ClevaPolytech/Arduino-Project/OralFinal/PolyShop.pdf

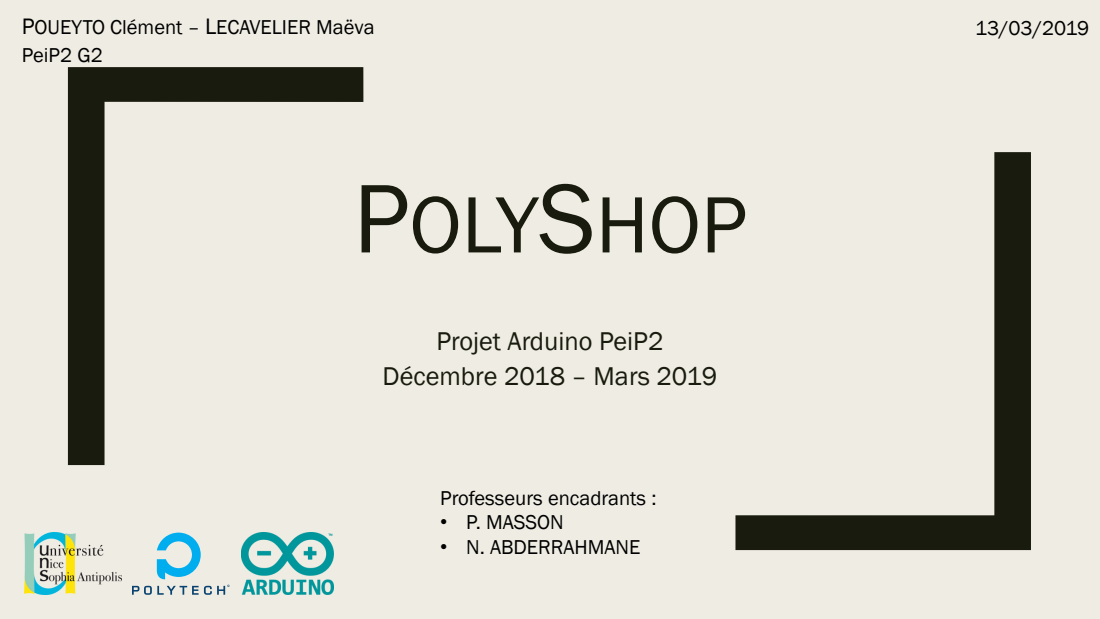
[picture p85: page 1]
POLYSHOP; Projet Arduino PeiP2 Décembre 2018 – Mars 2019; Professeurs encadrants : • P. MASSON • N. ABDERRAHMANE

POUEYTO Clément – LECAVELIER Maëva
PeiP2 G2

## Sommaire

■ Notre sujet
■ Objectifs initiaux
■ Comment ça fonctionne ?
■ De l’idée à la conception ■ Plannings
■ Conclusion

Notre sujet

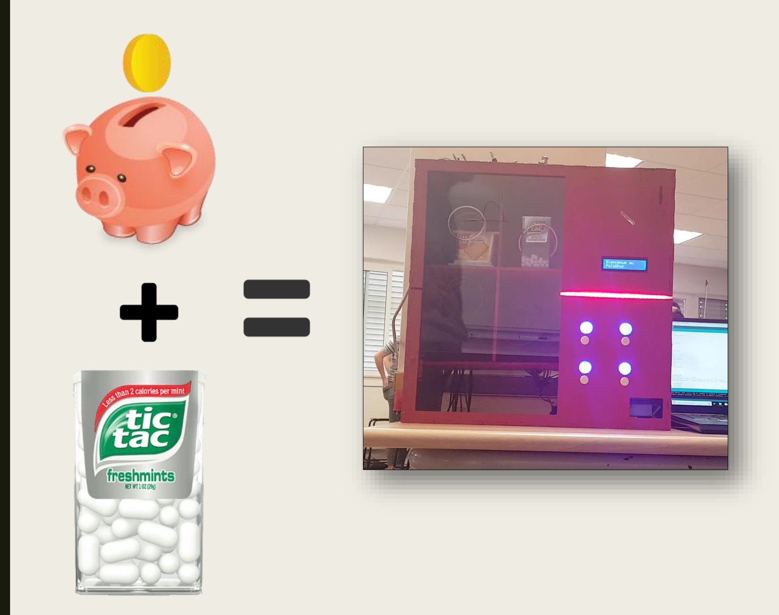
[picture p86: figure]

Monnayeur
Lumière
Barre de chargement
Ecran LCD
Distributeur de nourriture
Possibilité de sélectionner le snack voulu

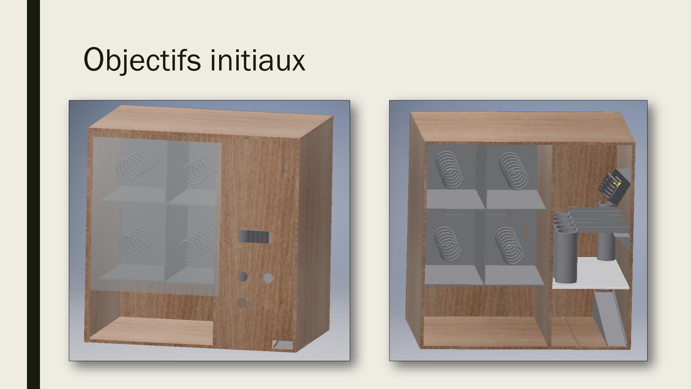
[picture p87: page 4]

Objectifs initiaux

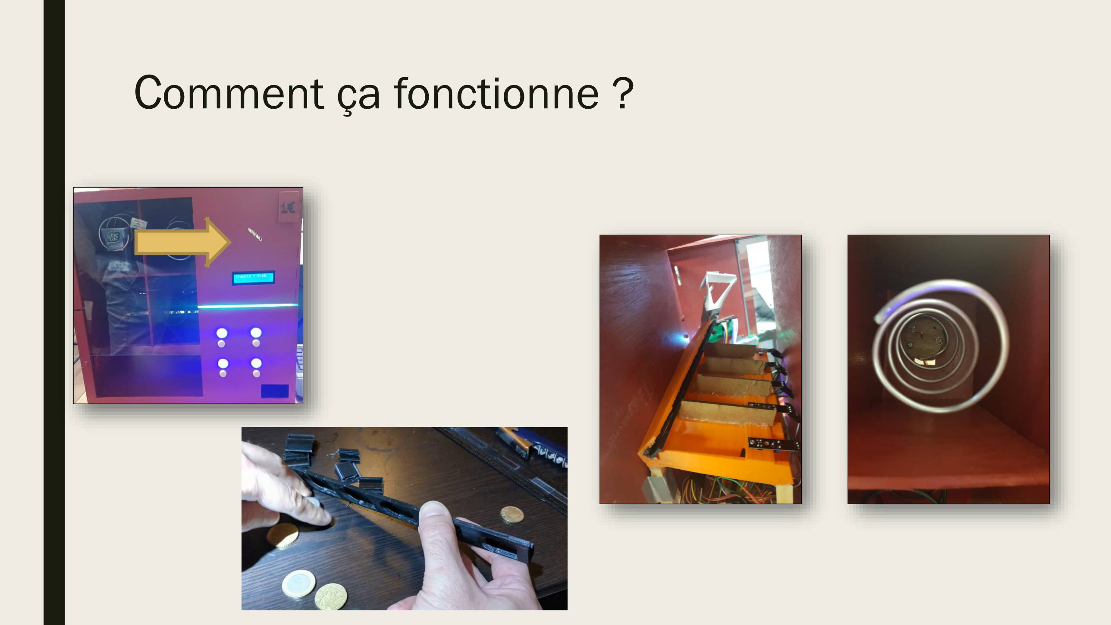
[picture p88: page 5]

Comment ça fonctionne ?

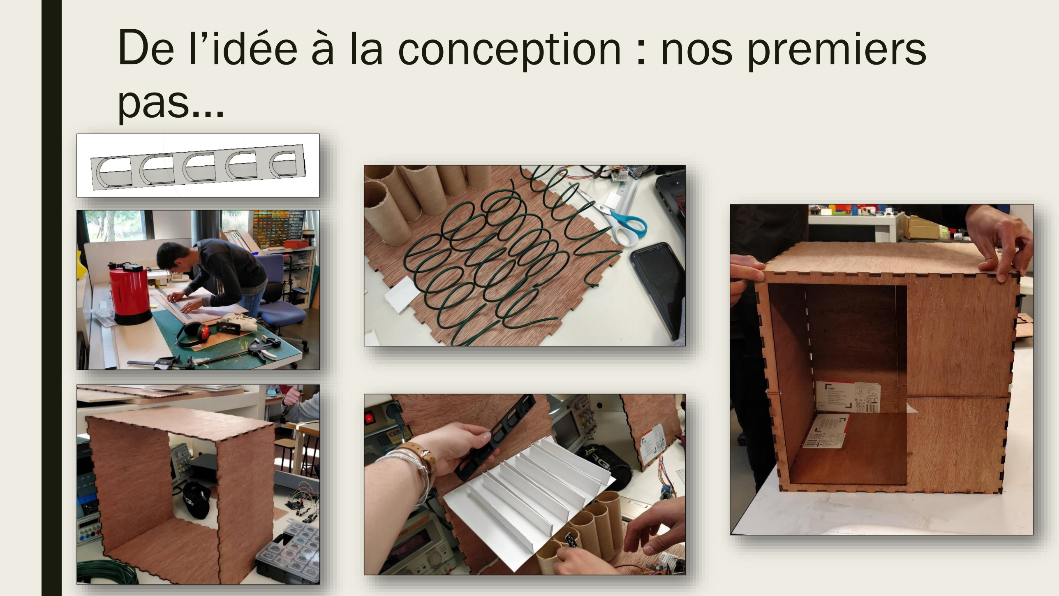
[picture p89: page 6]

De l’idée à la conception : nos premiers pas…

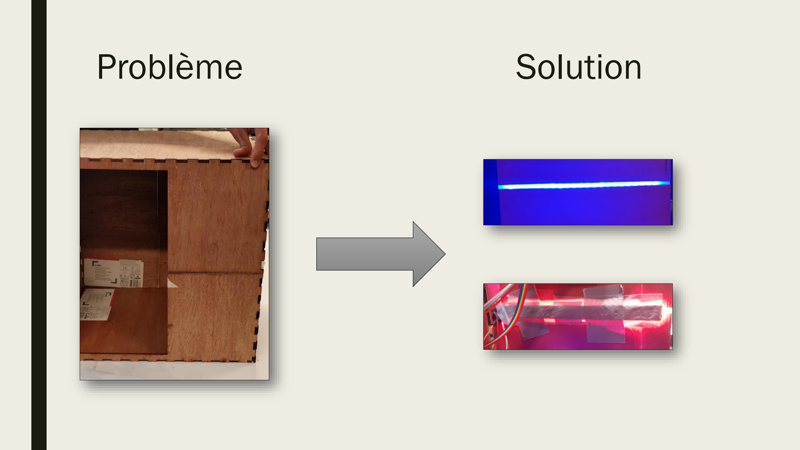
[picture p90: page 7]

Problème | Solution

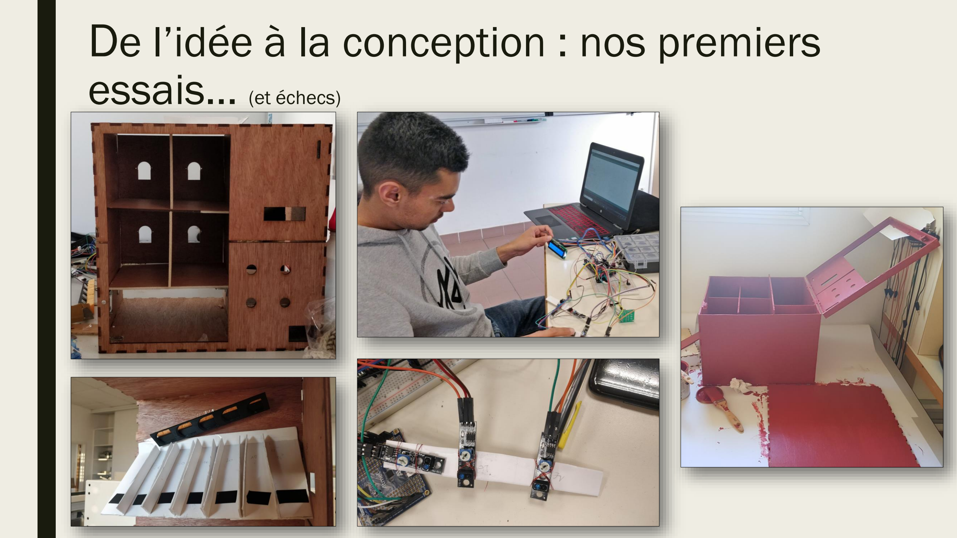
[picture p91: page 8]

De l’idée à la conception : nos premiers

essais… (et échecs)

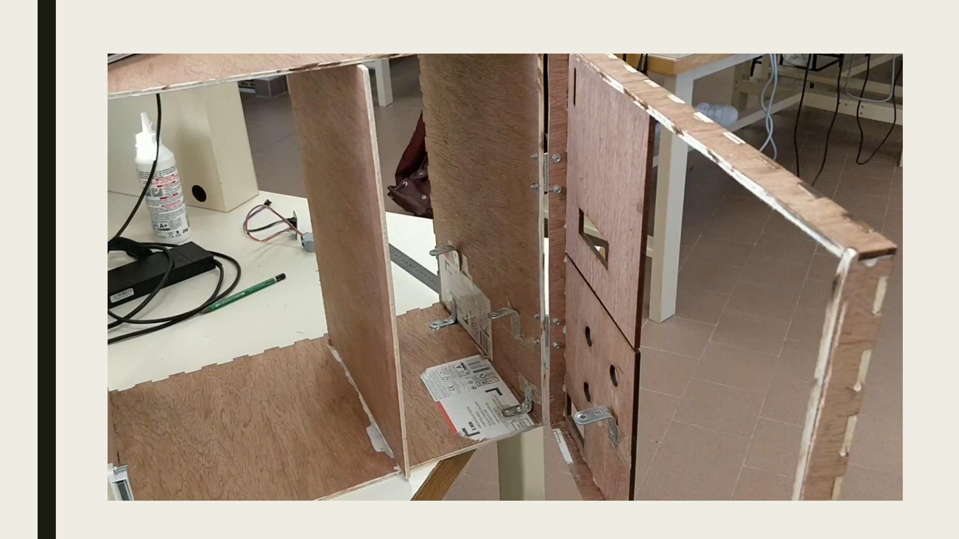
[picture p92: page 9]

Problème | Solution

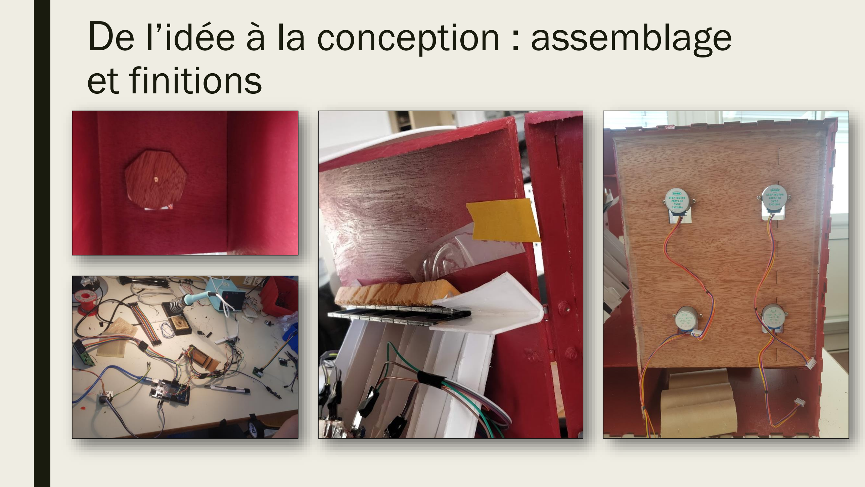
[picture p93: page 10]

De l’idée à la conception : assemblage et finitions

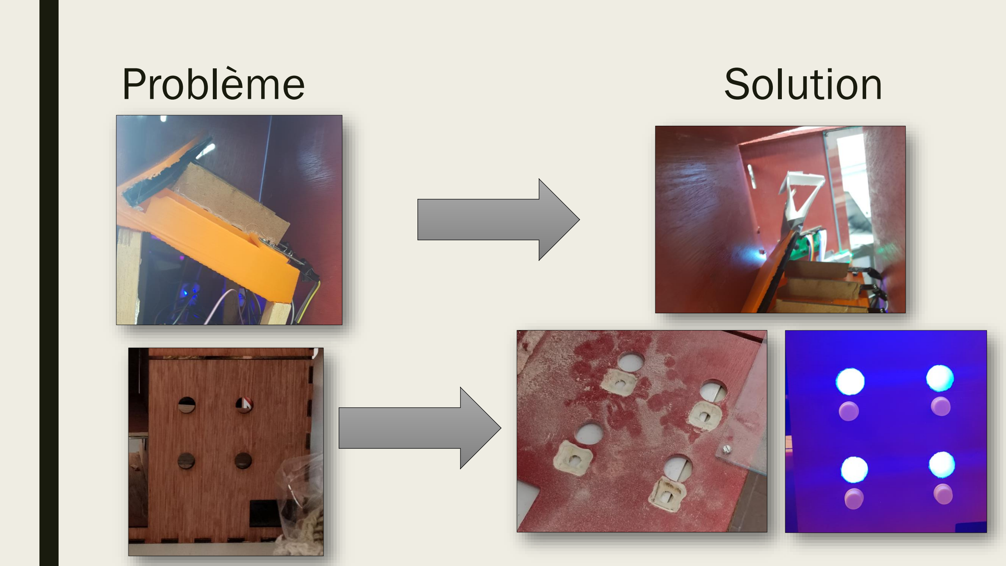
[picture p94: page 11]

Problème | Solution

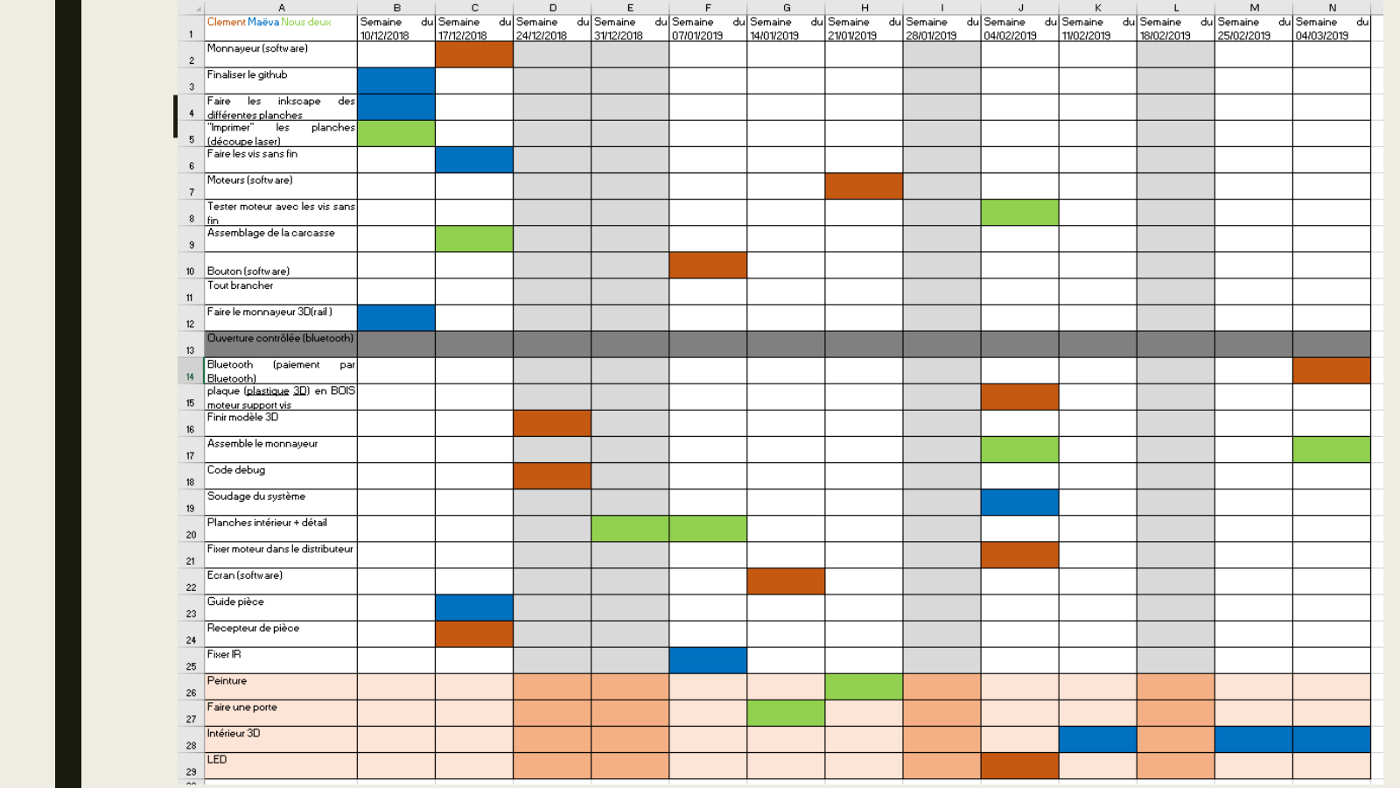
[picture p95: page 12]

Plannings

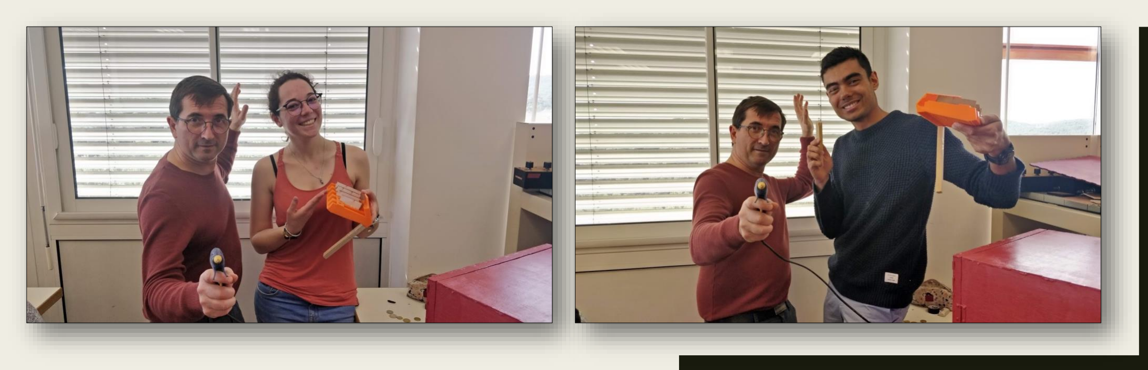
[picture p96: figure]

### CONCLUSION
