ClevaPolytech/Arduino-Project/Plannings/planning_initial.pdf

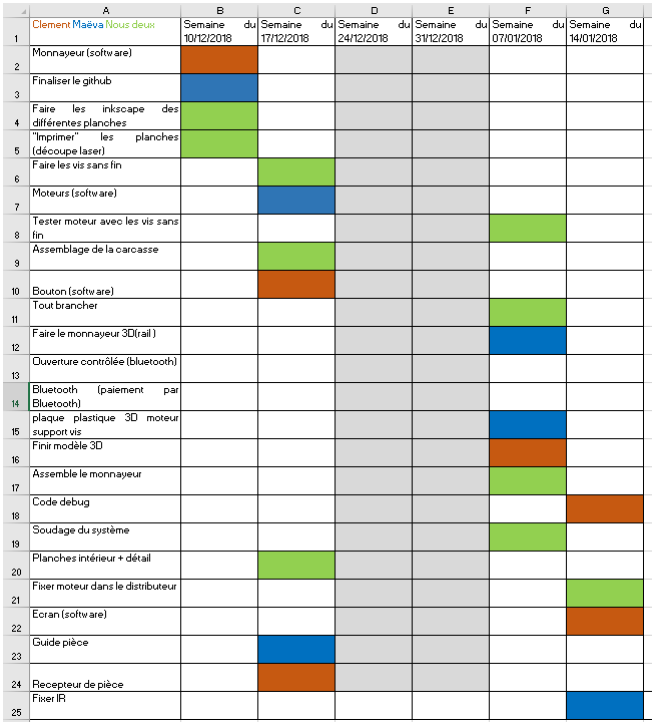
[picture p115: figure]
