ClevaPolytech/Arduino-Project/Photos/20181210_143604.jpg

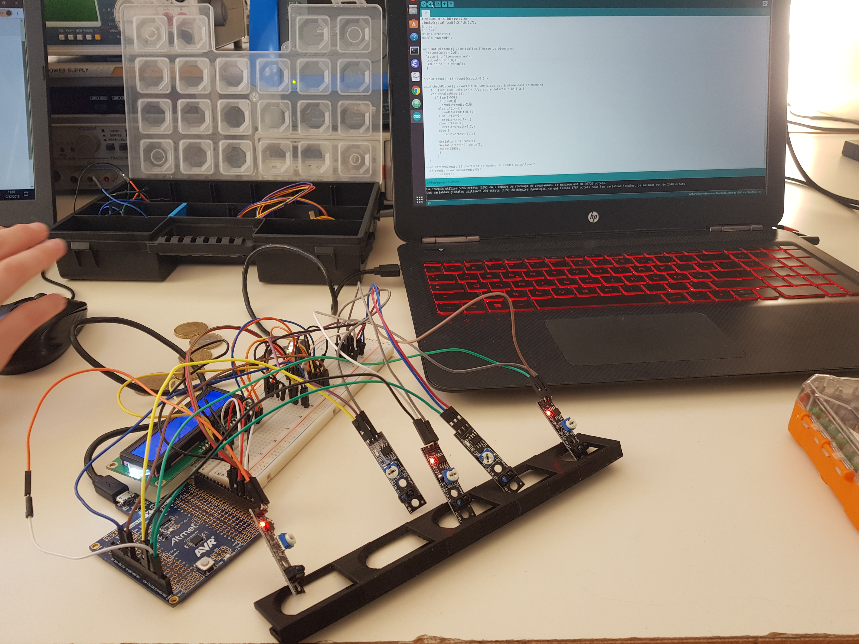
Photos/20181210_143604.jpg
