ClevaPolytech/Arduino-Project/Photos/20181210_154950.jpg

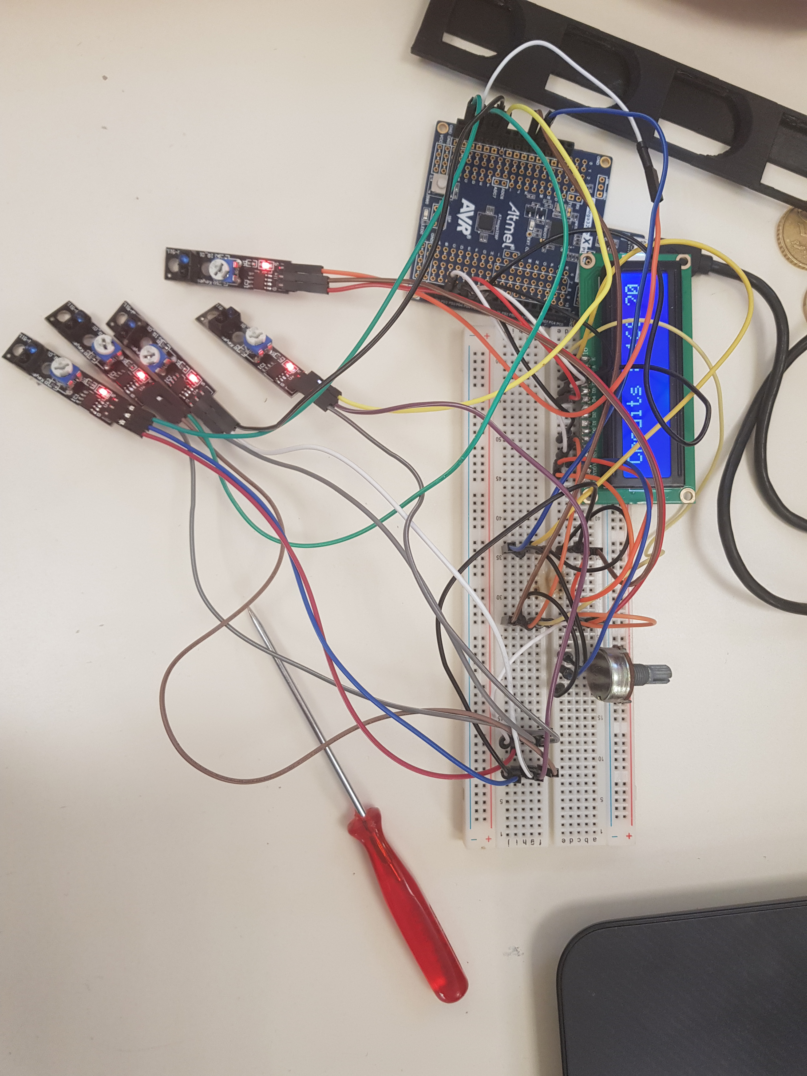
Photos/20181210_154950.jpg
