ClevaPolytech/Arduino-Project/Photos/20181214_130924.jpg

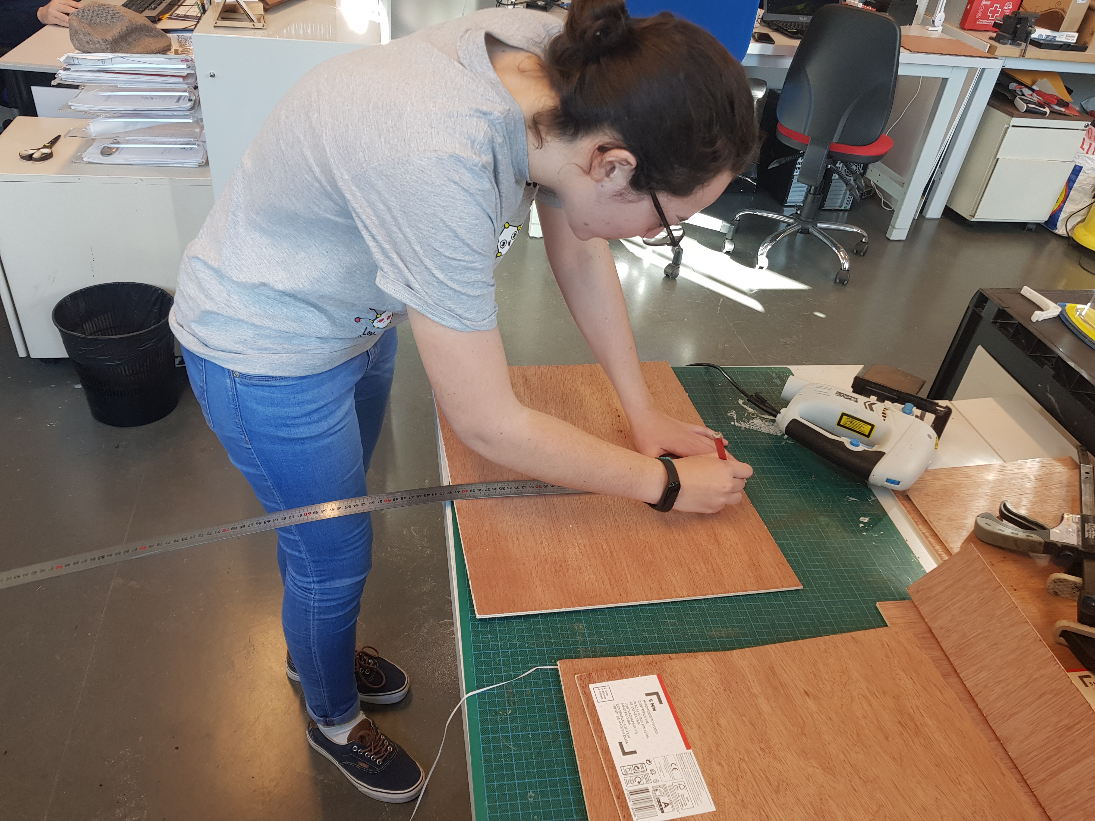
Photos/20181214_130924.jpg
