ClevaPolytech/Arduino-Project/Photos/20181217_135600.jpg

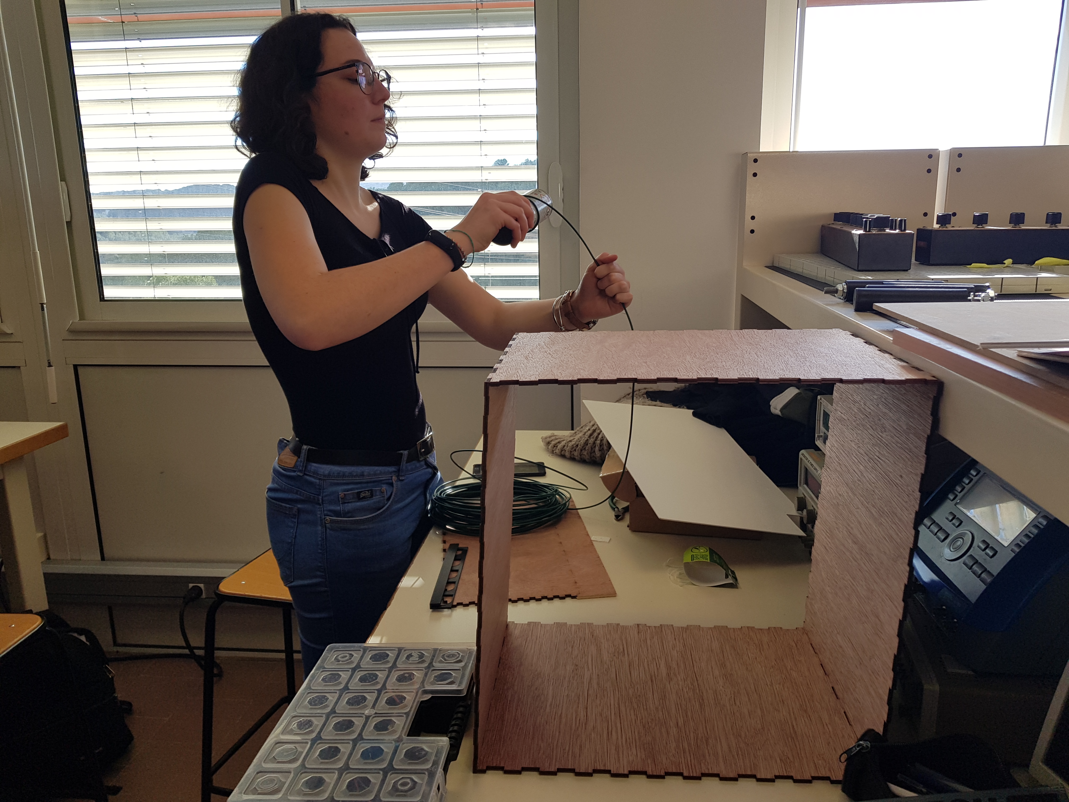
Photos/20181217_135600.jpg
