ClevaPolytech/Arduino-Project/Photos/20181217_135611.jpg

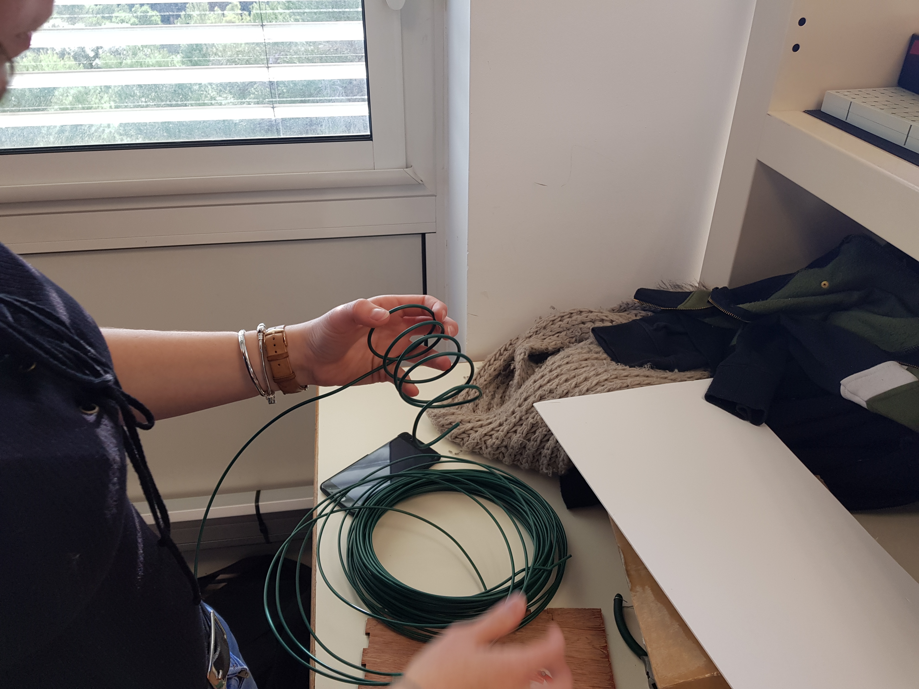
Photos/20181217_135611.jpg
