ClevaPolytech/Arduino-Project/Photos/20181217_135612.jpg

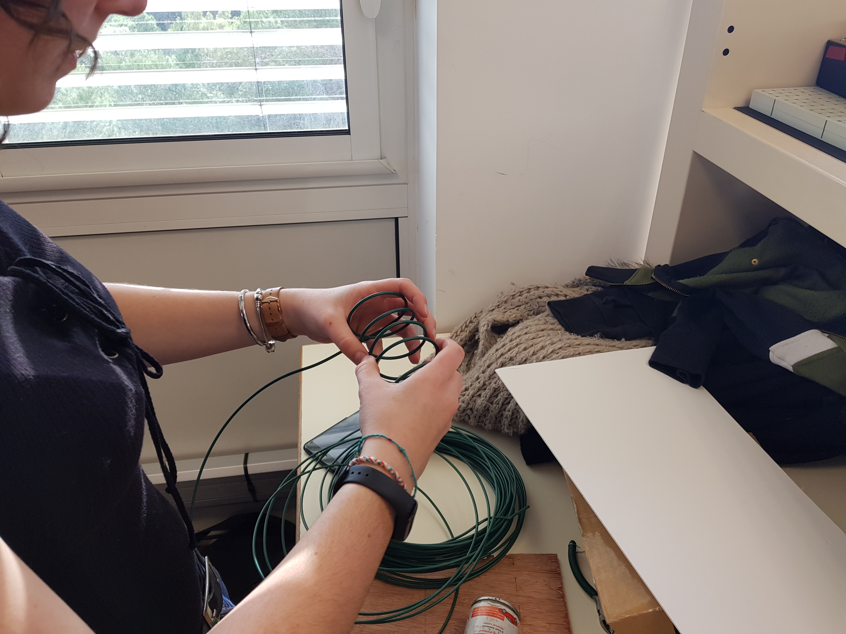
Photos/20181217_135612.jpg
