ClevaPolytech/Arduino-Project/Photos/20181217_142027.jpg

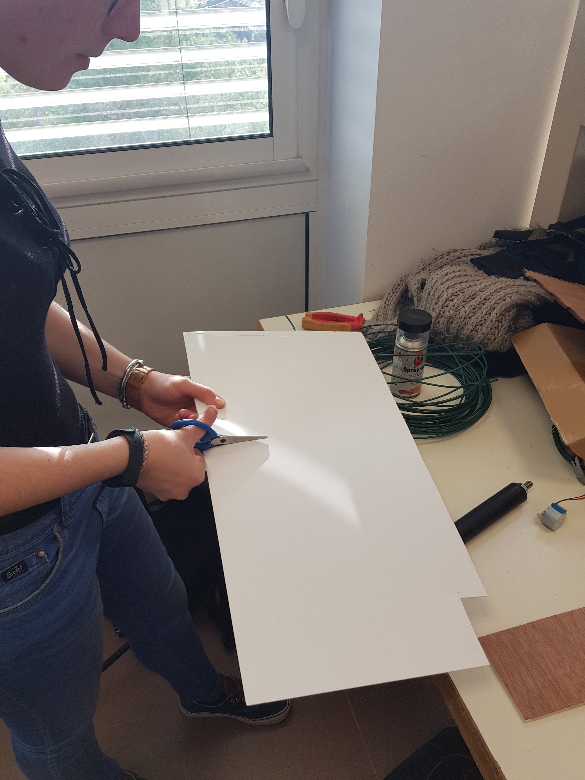
Photos/20181217_142027.jpg
