ClevaPolytech/Arduino-Project/Photos/20181217_142030.jpg

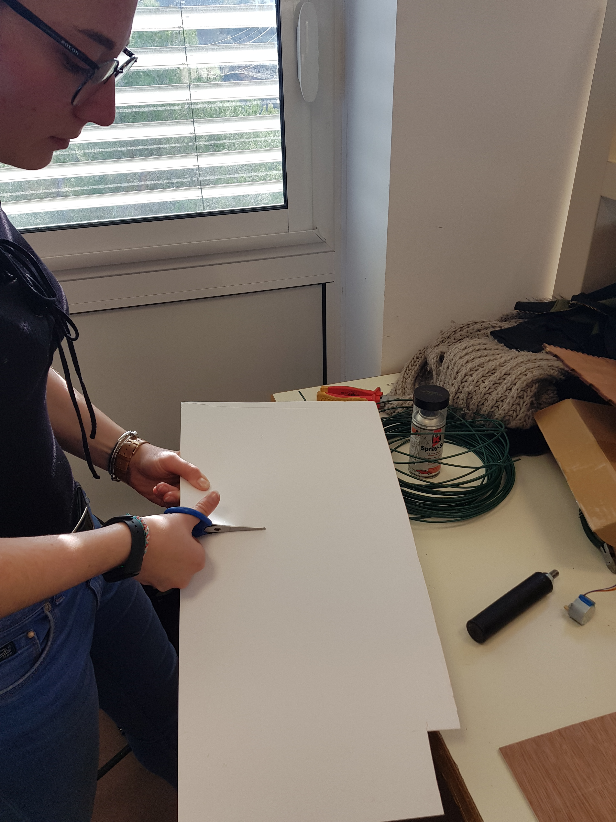
Photos/20181217_142030.jpg
