ClevaPolytech/Arduino-Project/Photos/20181217_143016.jpg

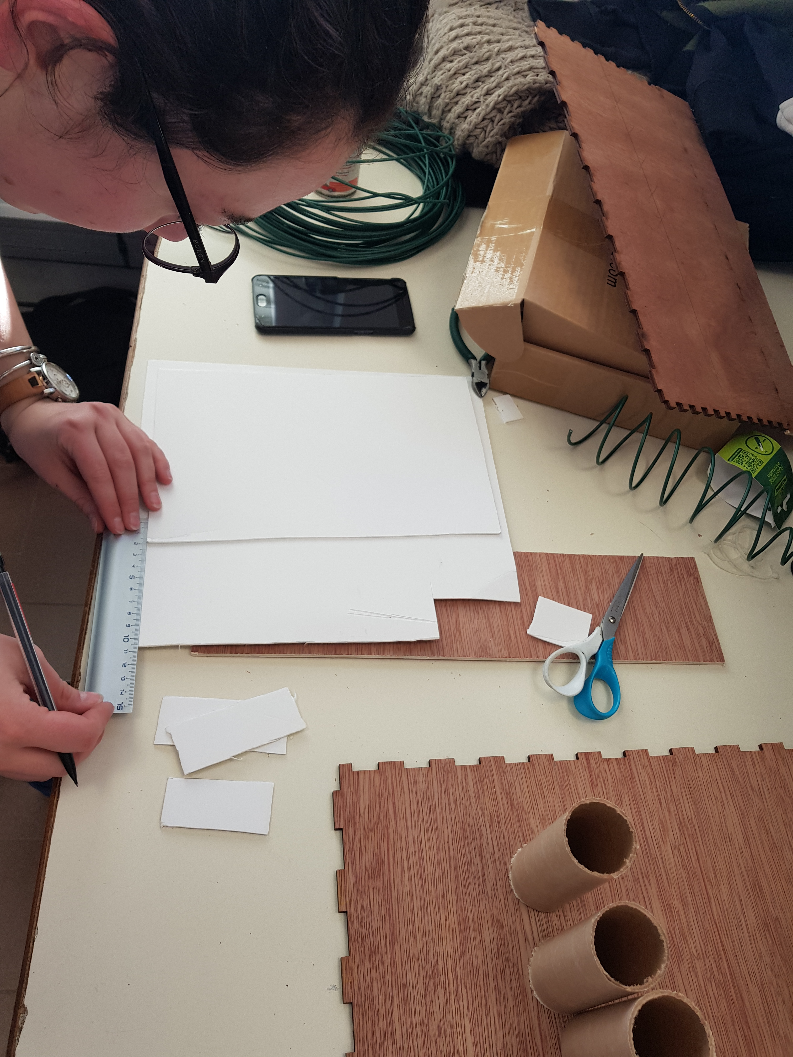
Photos/20181217_143016.jpg
