ClevaPolytech/Arduino-Project/Photos/20181219_123023.jpg

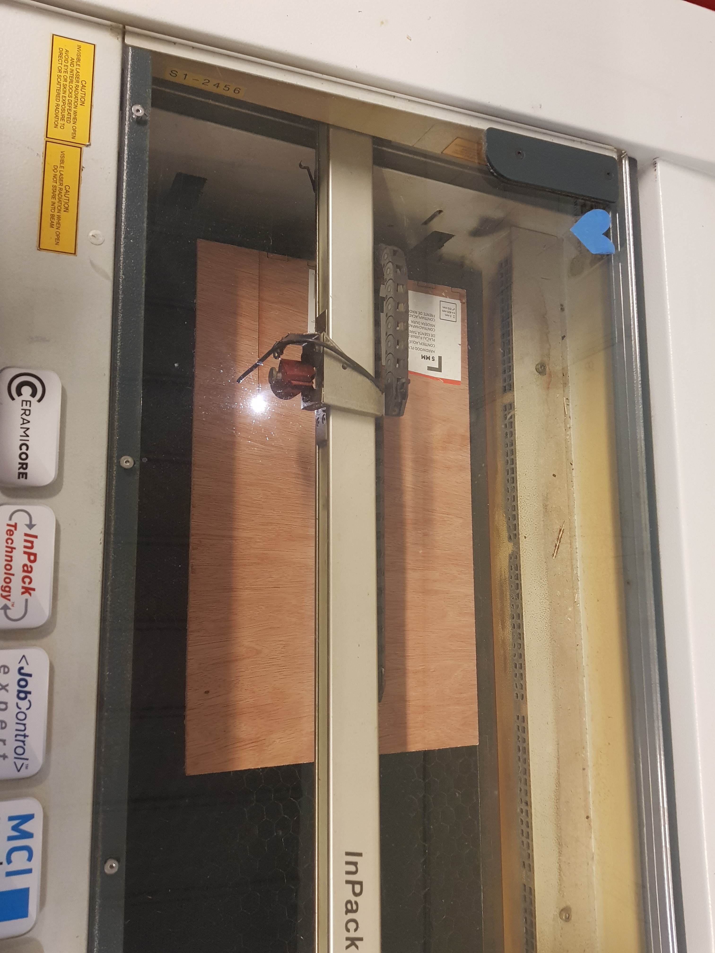
Photos/20181219_123023.jpg
