ClevaPolytech/Arduino-Project/Photos/20181219_130258.jpg

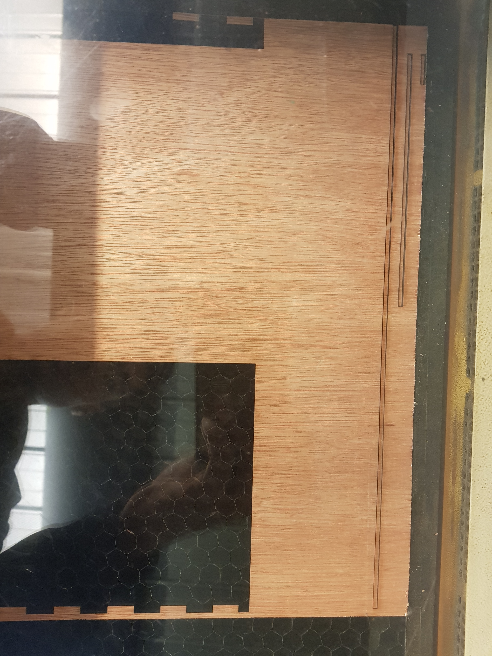
Photos/20181219_130258.jpg
