ClevaPolytech/Arduino-Project/Photos/20181219_131254.jpg

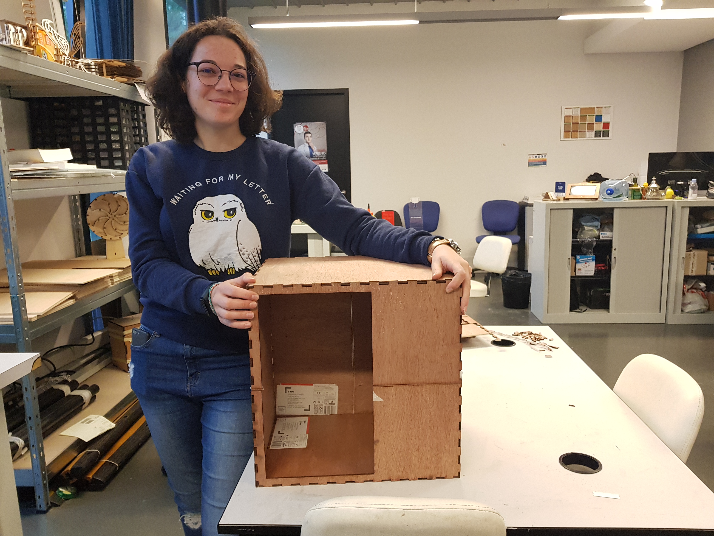
Photos/20181219_131254.jpg
