ClevaPolytech/Arduino-Project/Photos/20190103_140715.jpg

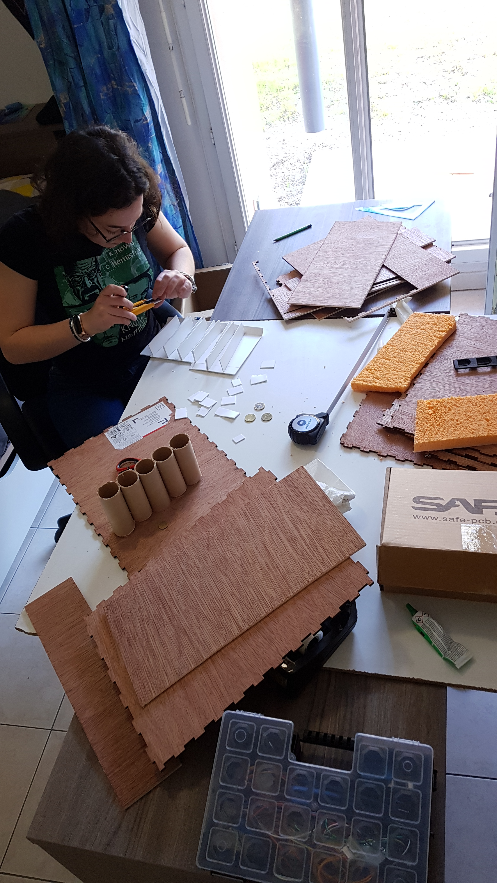
Photos/20190103_140715.jpg
