ClevaPolytech/Arduino-Project/Photos/20190103_140730.jpg

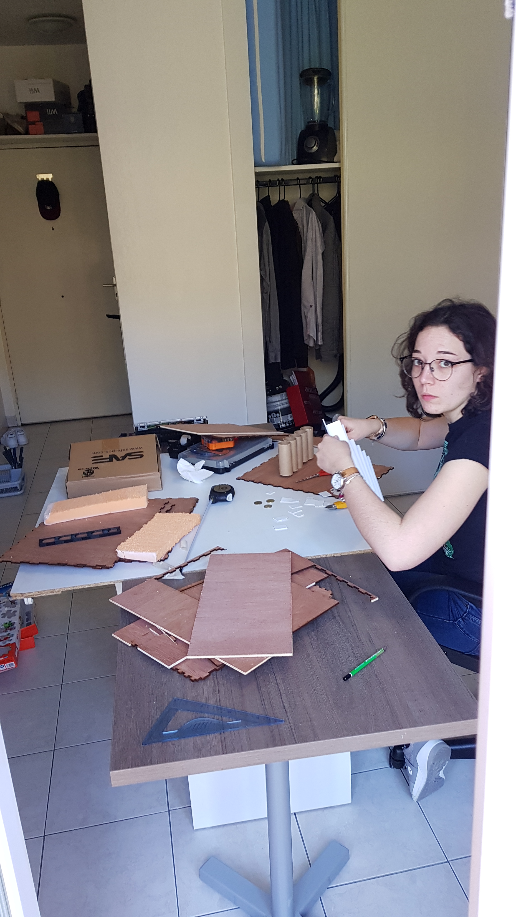
Photos/20190103_140730.jpg
