ClevaPolytech/Arduino-Project/Photos/20190103_140749.jpg

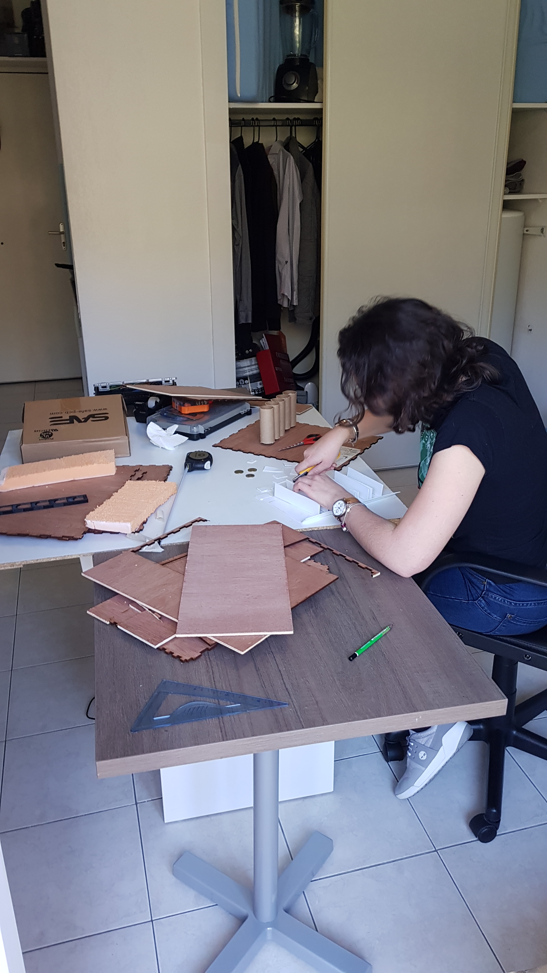
Photos/20190103_140749.jpg
