ClevaPolytech/Arduino-Project/Photos/20190103_145221.jpg

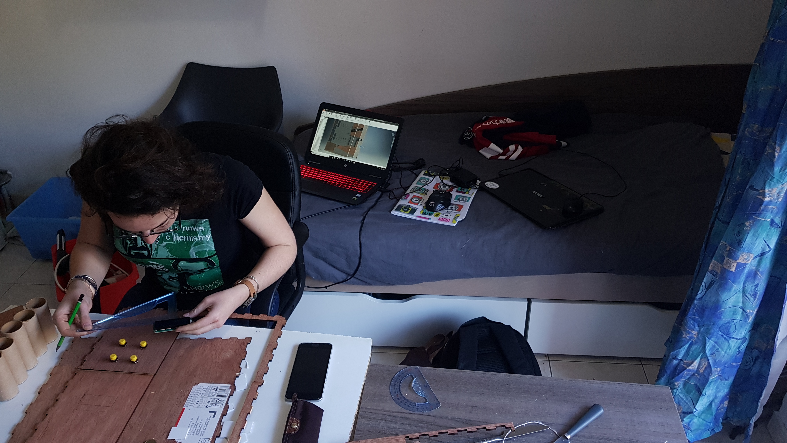
Photos/20190103_145221.jpg
