ClevaPolytech/Arduino-Project/Photos/20190103_183734.jpg

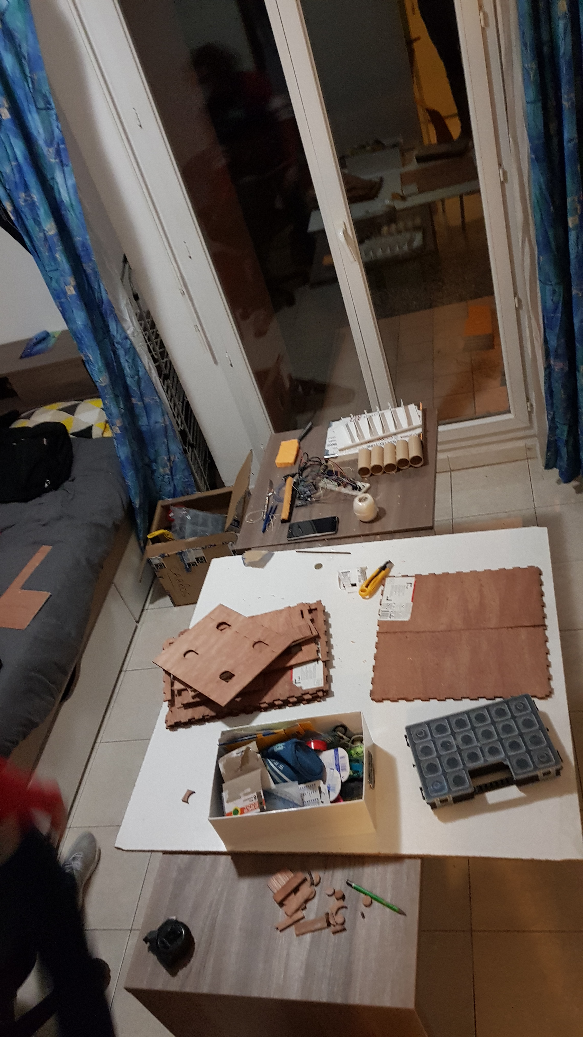
Photos/20190103_183734.jpg
