ClevaPolytech/Arduino-Project/Photos/20190103_183739.jpg

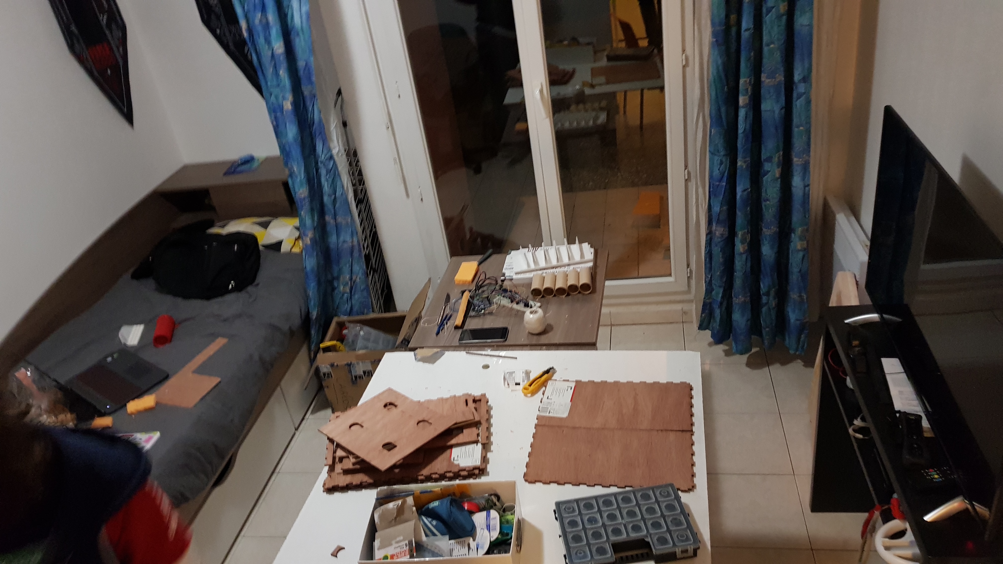
Photos/20190103_183739.jpg
