ClevaPolytech/Arduino-Project/Photos/20190103_183746.jpg

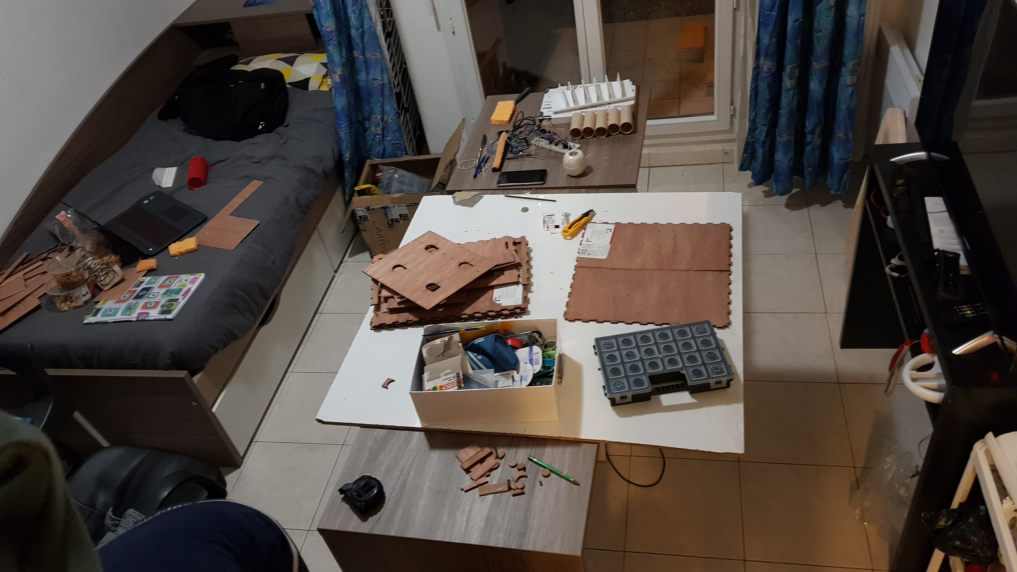
Photos/20190103_183746.jpg
