ClevaPolytech/Arduino-Project/Photos/20190107_112707.jpg

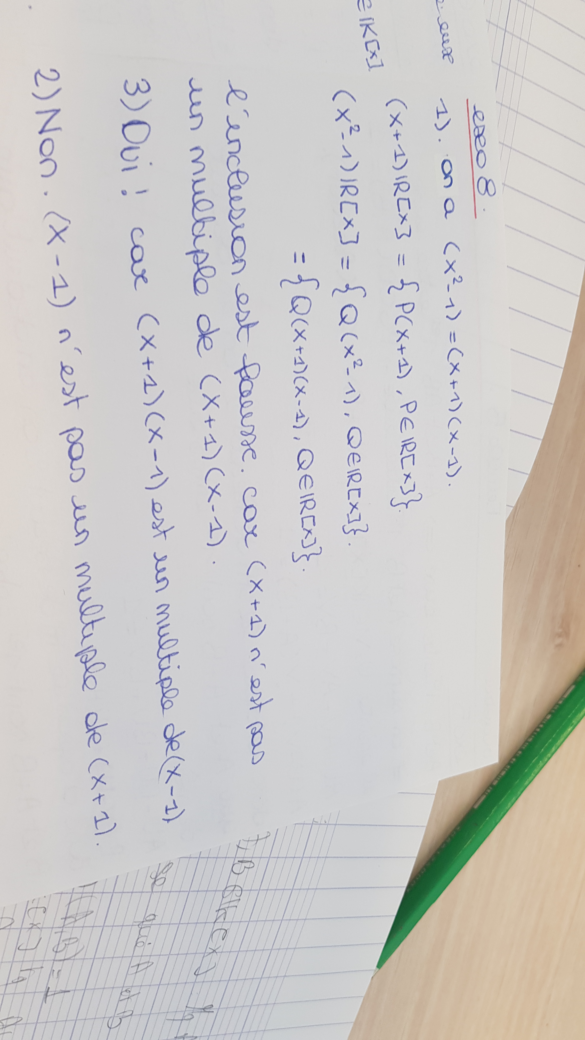
Photos/20190107_112707.jpg
