ClevaPolytech/Arduino-Project/Photos/20190107_141950.jpg

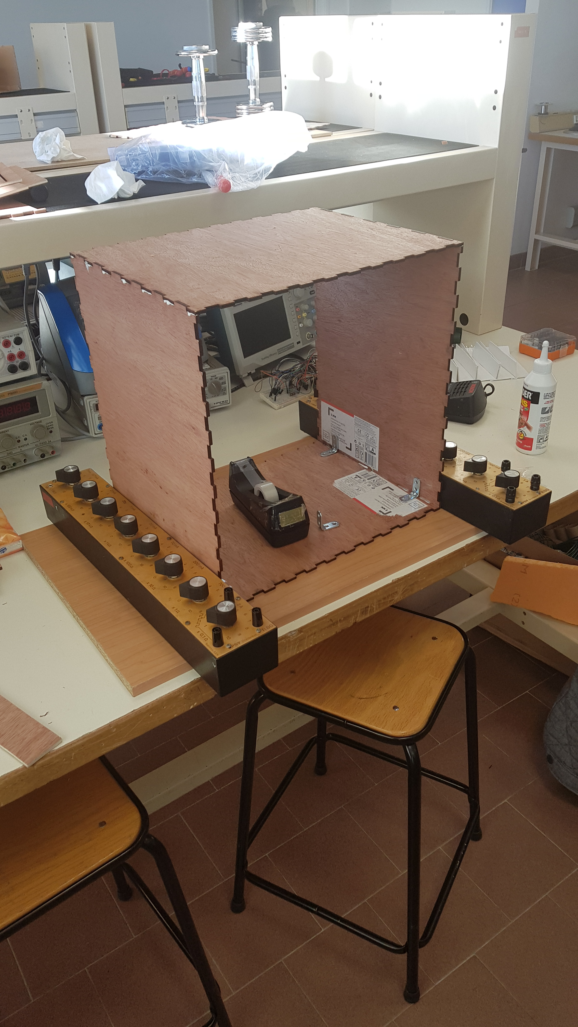
Photos/20190107_141950.jpg
