ClevaPolytech/Arduino-Project/Photos/20190107_161657.jpg

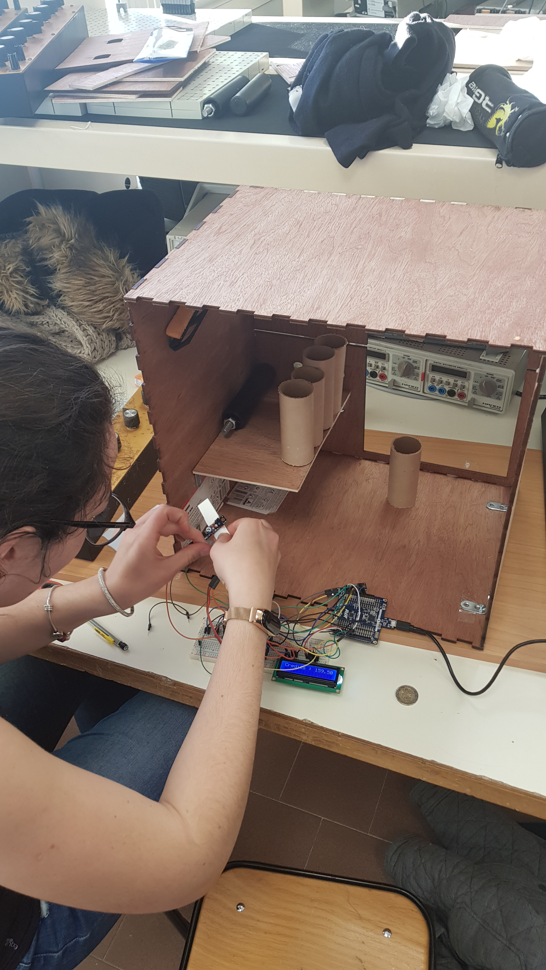
Photos/20190107_161657.jpg
