ClevaPolytech/Arduino-Project/Photos/20190107_164838.jpg

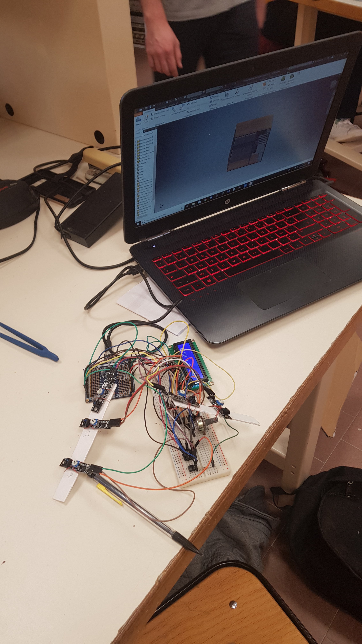
Photos/20190107_164838.jpg
