ClevaPolytech/Arduino-Project/Photos/20190107_164943.jpg

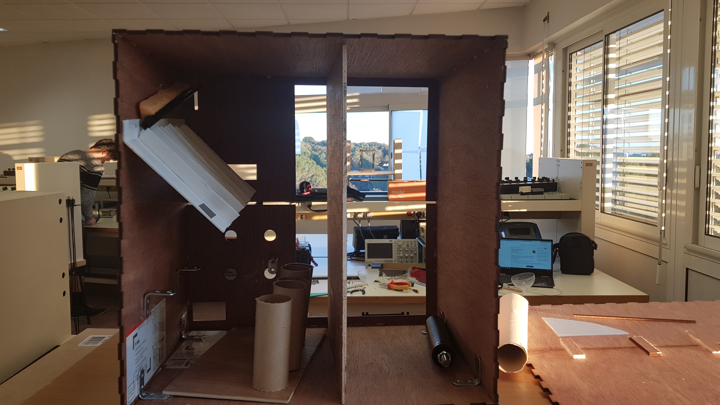
Photos/20190107_164943.jpg
