ClevaPolytech/Arduino-Project/Photos/20190107_164952.jpg

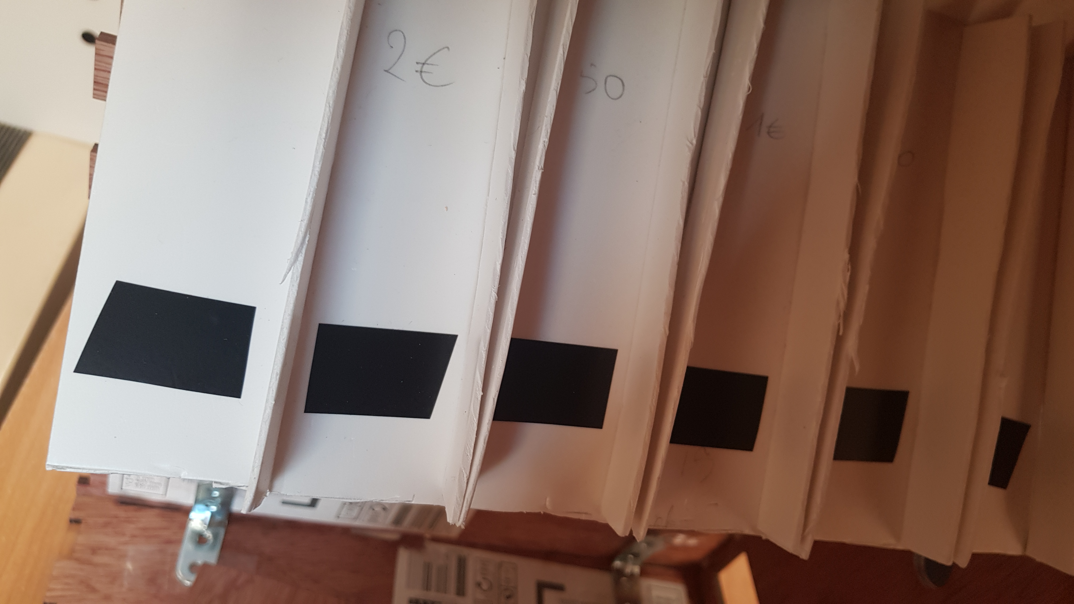
Photos/20190107_164952.jpg
