ClevaPolytech/Arduino-Project/Photos/20190114_145928.jpg

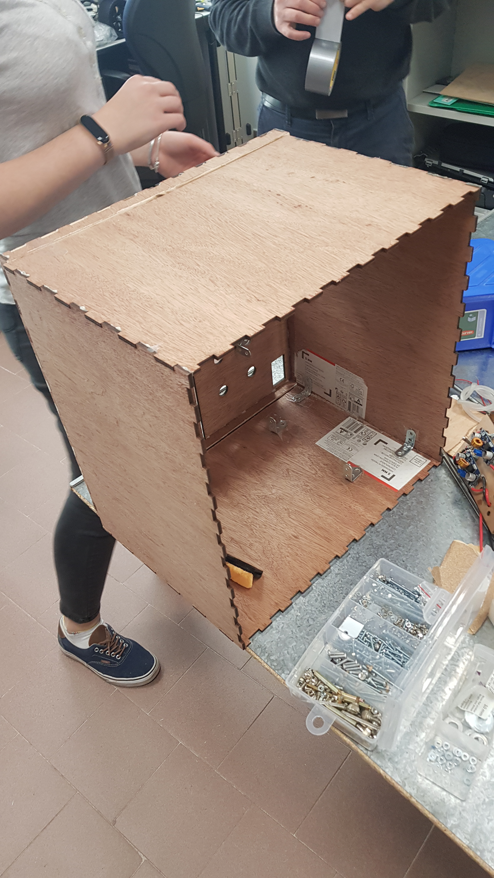
Photos/20190114_145928.jpg
