ClevaPolytech/Arduino-Project/Photos/20190114_150440.jpg

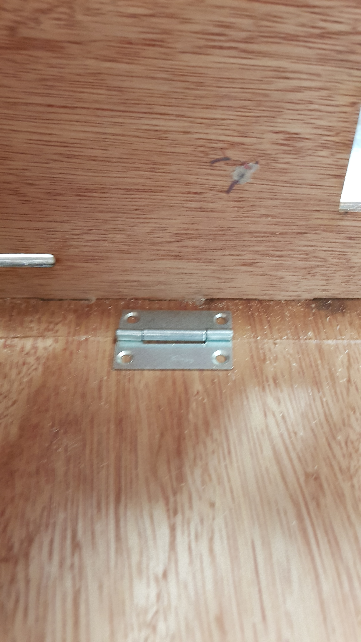
Photos/20190114_150440.jpg
