ClevaPolytech/Arduino-Project/Photos/20190114_150518.jpg

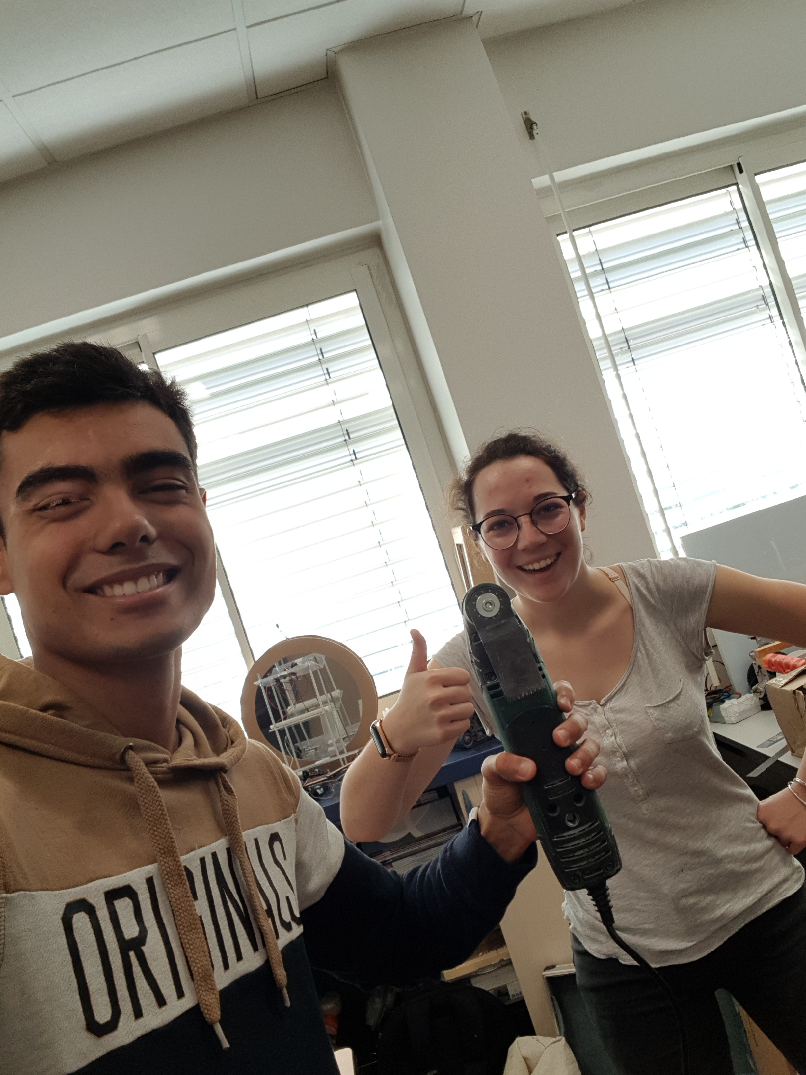
Photos/20190114_150518.jpg
