ClevaPolytech/Arduino-Project/Photos/20190114_151002.jpg

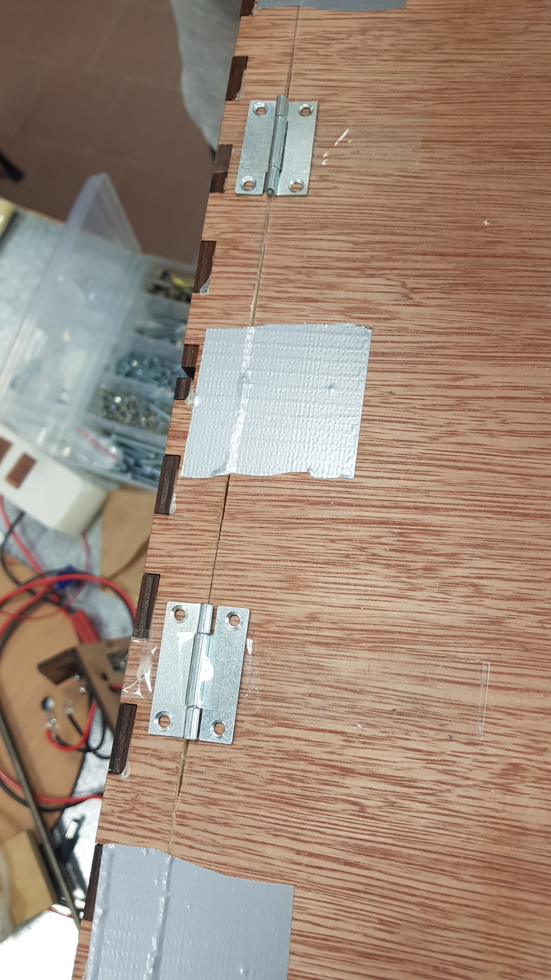
Photos/20190114_151002.jpg
