ClevaPolytech/Arduino-Project/Photos/20190114_151236.jpg

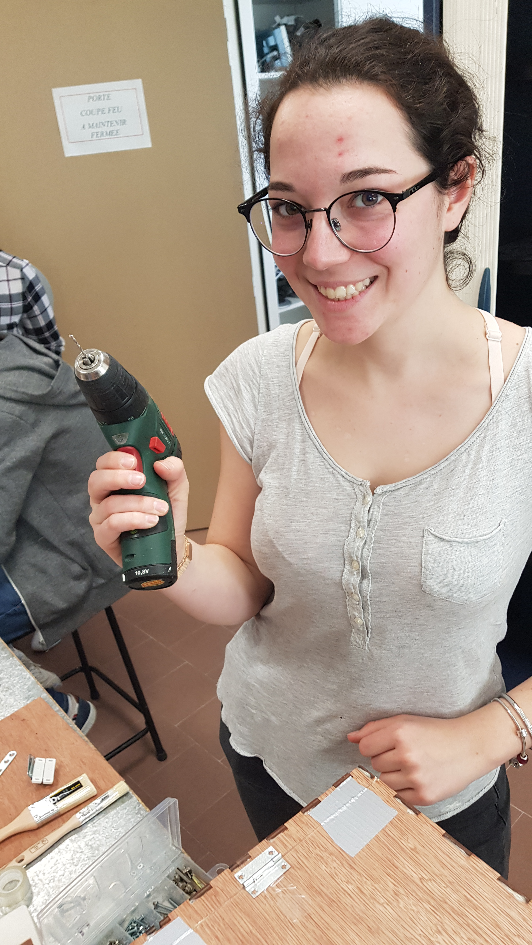
Photos/20190114_151236.jpg
