ClevaPolytech/Arduino-Project/Photos/20190114_151253.jpg

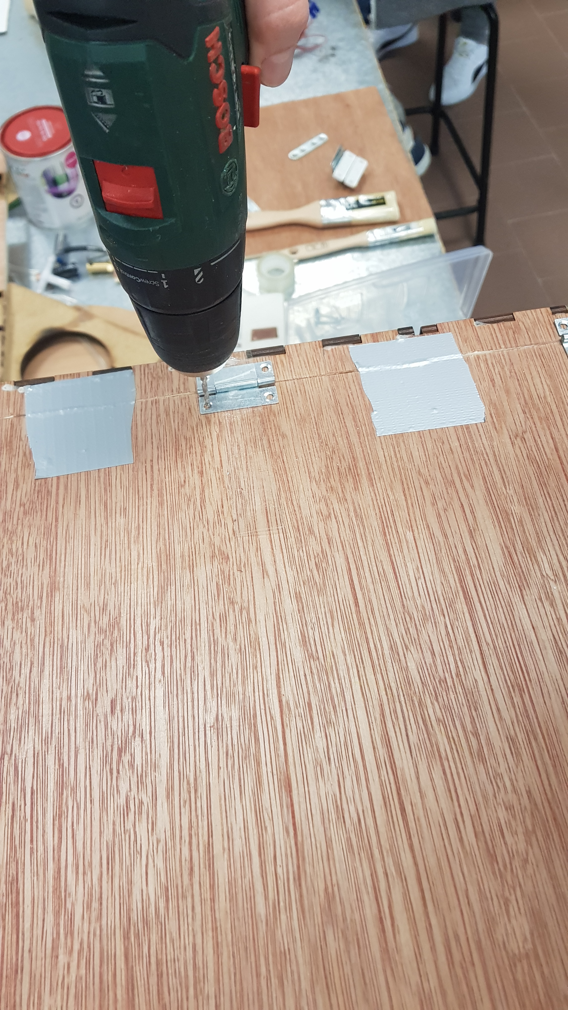
Photos/20190114_151253.jpg
