ClevaPolytech/Arduino-Project/Photos/20190114_163101.jpg

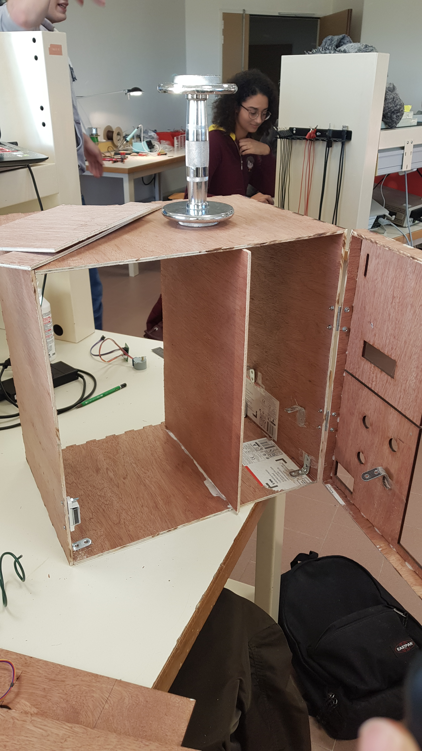
Photos/20190114_163101.jpg
