ClevaPolytech/Arduino-Project/Photos/20190114_163104.jpg

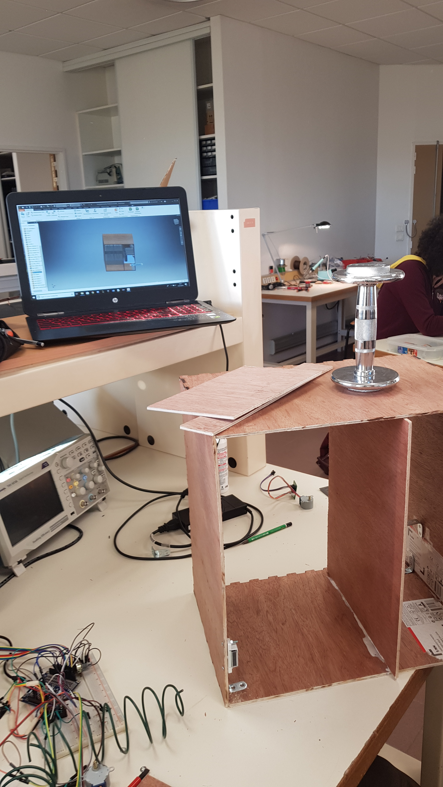
Photos/20190114_163104.jpg
