ClevaPolytech/Arduino-Project/Photos/20190114_163140.jpg

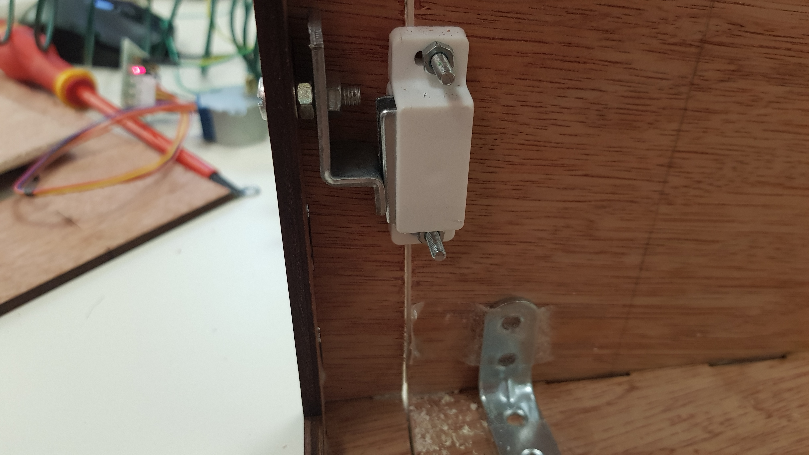
Photos/20190114_163140.jpg
