ClevaPolytech/Arduino-Project/Photos/20190114_165055.jpg

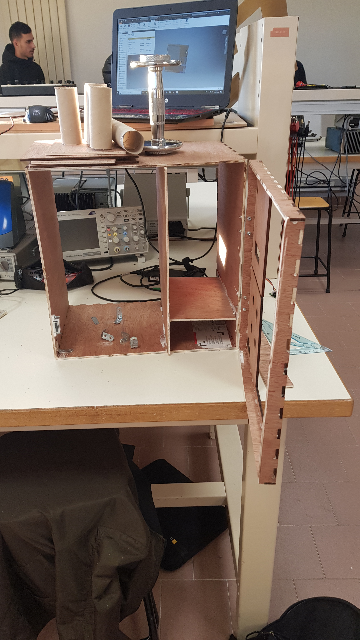
Photos/20190114_165055.jpg
