ClevaPolytech/Arduino-Project/Photos/20190114_165440.jpg

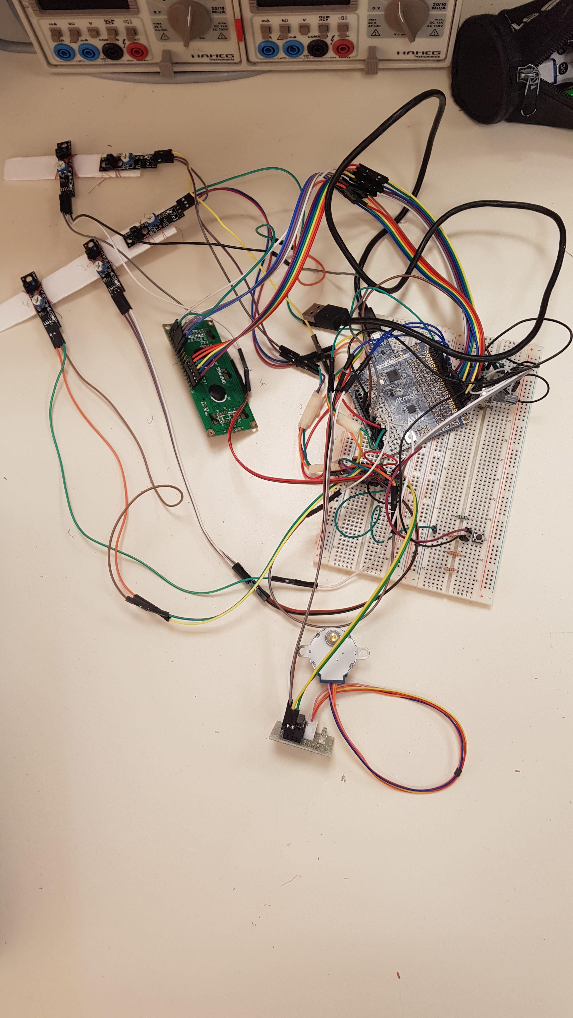
Photos/20190114_165440.jpg
