ClevaPolytech/Arduino-Project/Photos/20190118_145727.jpg

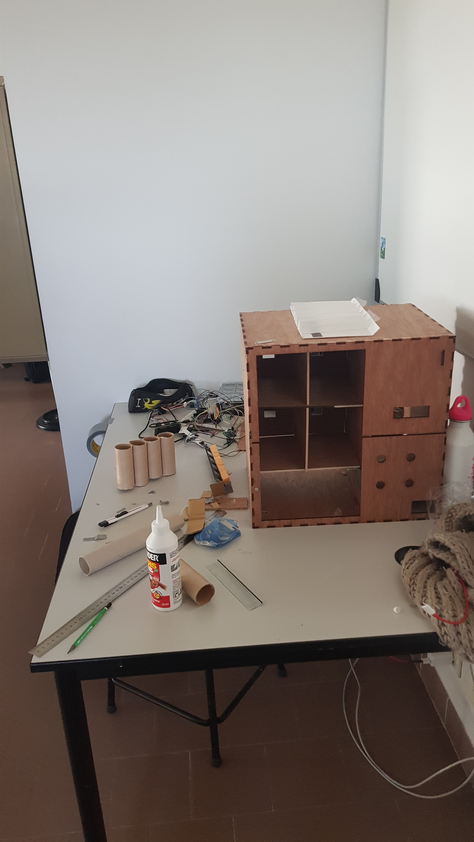
Photos/20190118_145727.jpg
