ClevaPolytech/Arduino-Project/Photos/20190118_145731.jpg

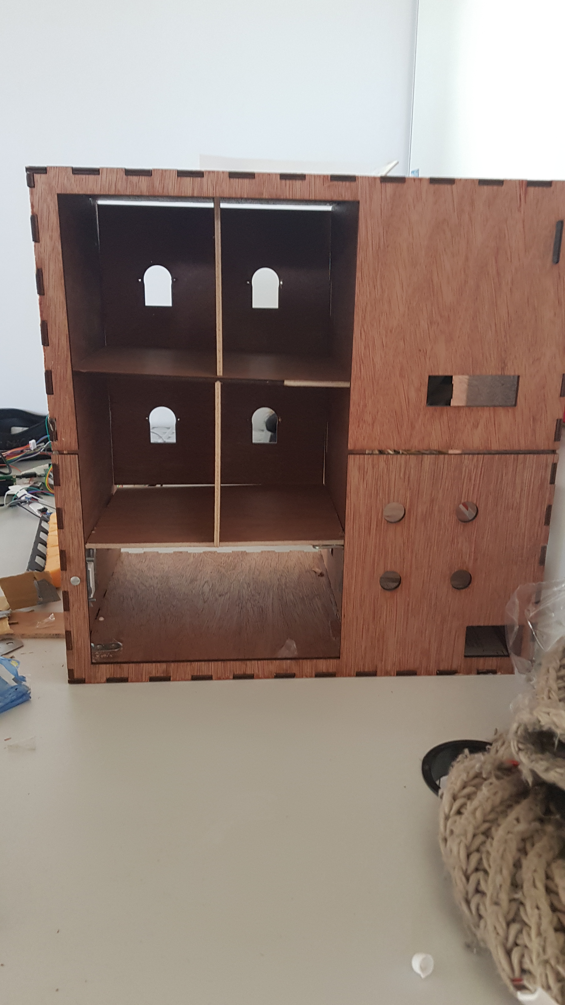
Photos/20190118_145731.jpg
