ClevaPolytech/Arduino-Project/Photos/20190118_160348.jpg

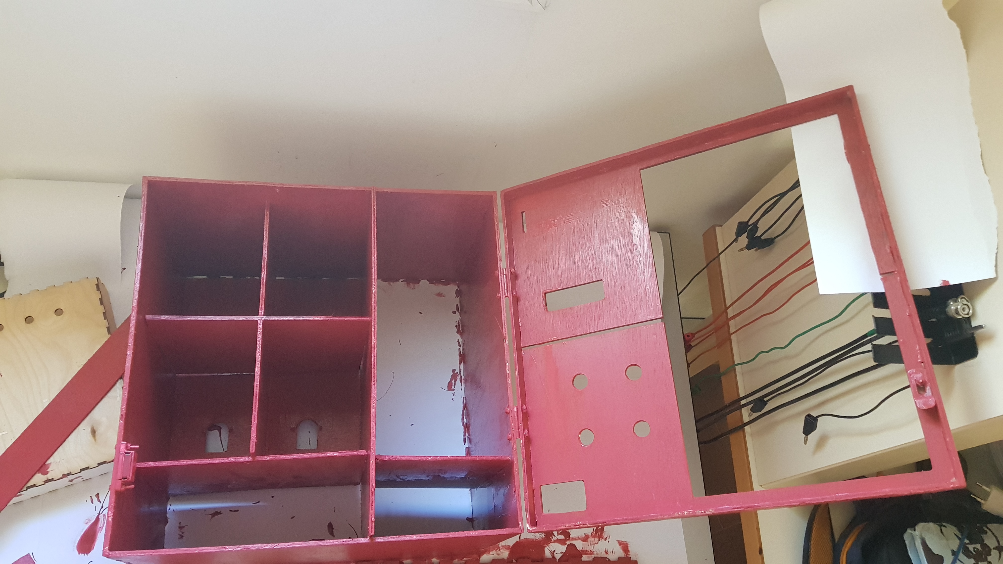
Photos/20190118_160348.jpg
