ClevaPolytech/Arduino-Project/Photos/20190118_160517.jpg

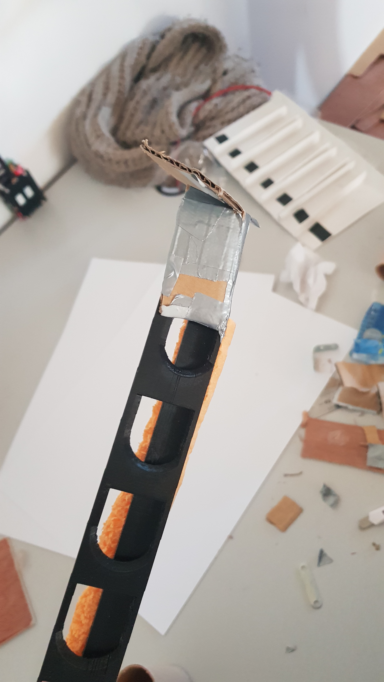
Photos/20190118_160517.jpg
