ClevaPolytech/Arduino-Project/Photos/20190123_104559.jpg

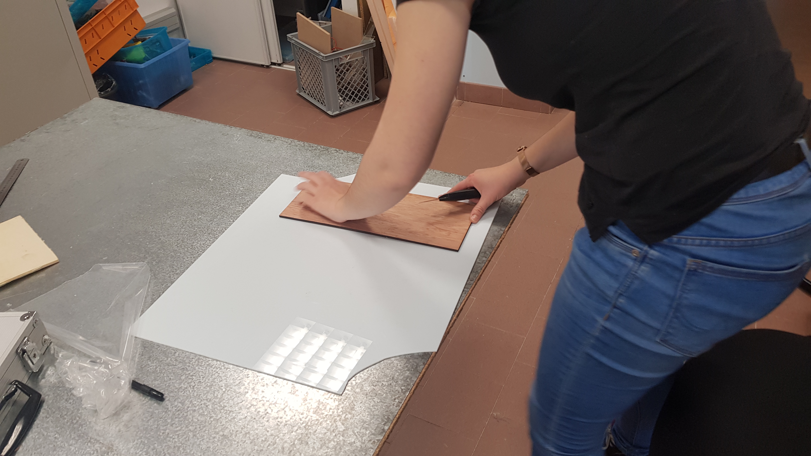
Photos/20190123_104559.jpg
