ClevaPolytech/Arduino-Project/Photos/20190123_104609.jpg

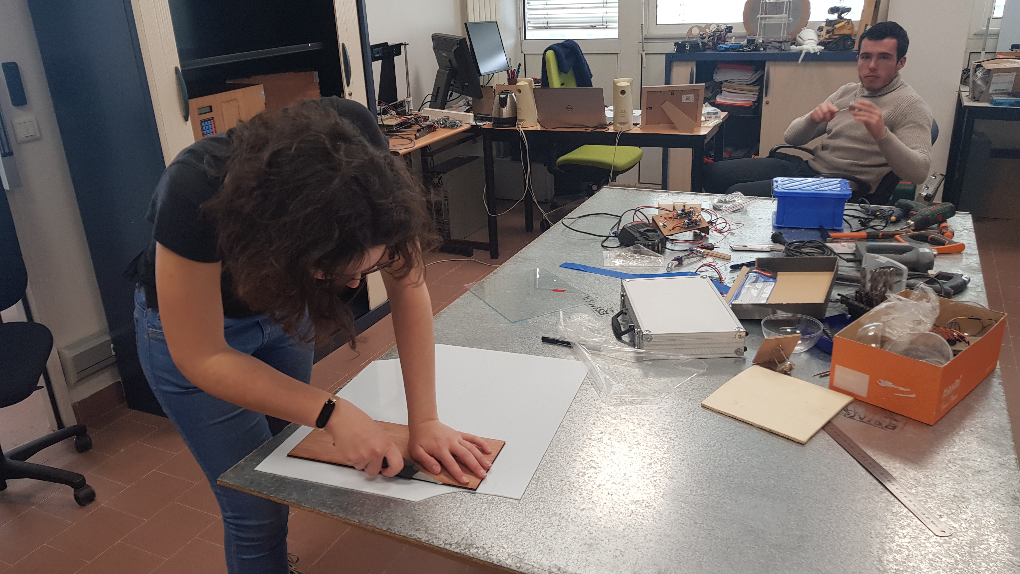
Photos/20190123_104609.jpg
