ClevaPolytech/Arduino-Project/Photos/20190123_104612.jpg

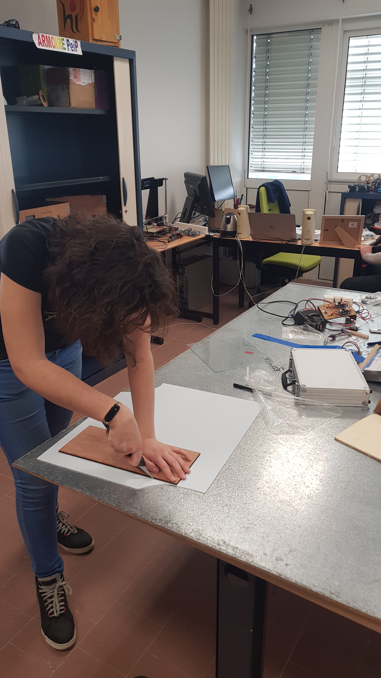
Photos/20190123_104612.jpg
