ClevaPolytech/Arduino-Project/Photos/20190123_104617.jpg

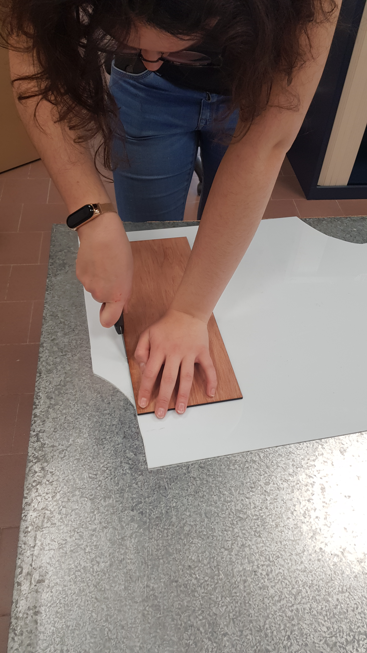
Photos/20190123_104617.jpg
