ClevaPolytech/Arduino-Project/Photos/20190123_132439.jpg

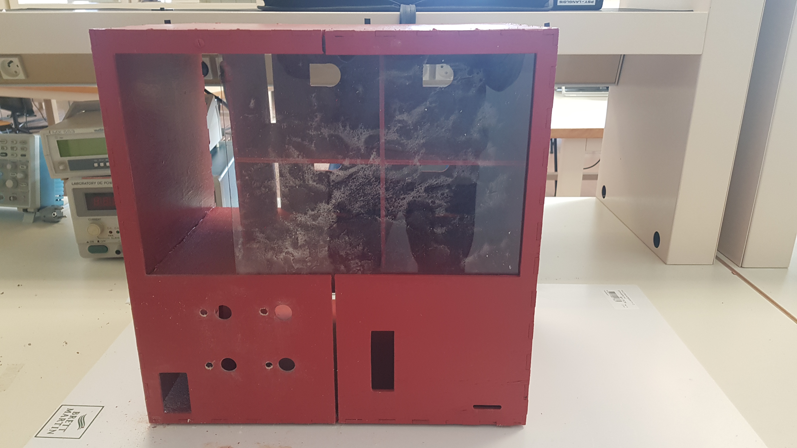
Photos/20190123_132439.jpg
