ClevaPolytech/Arduino-Project/Photos/20190123_132455.jpg

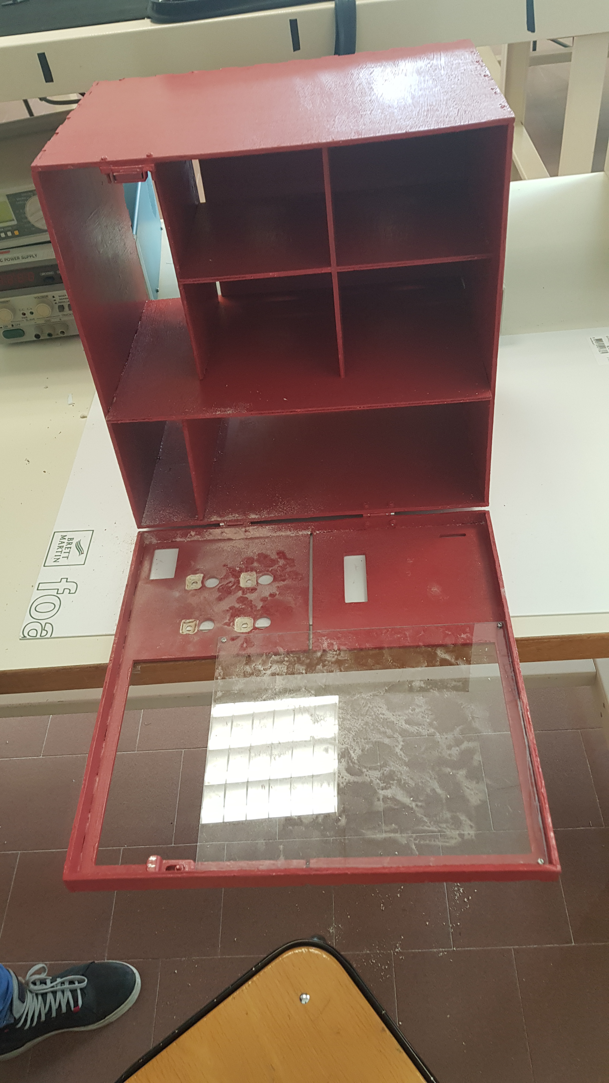
Photos/20190123_132455.jpg
