ClevaPolytech/Arduino-Project/Photos/20190208_111706.jpg

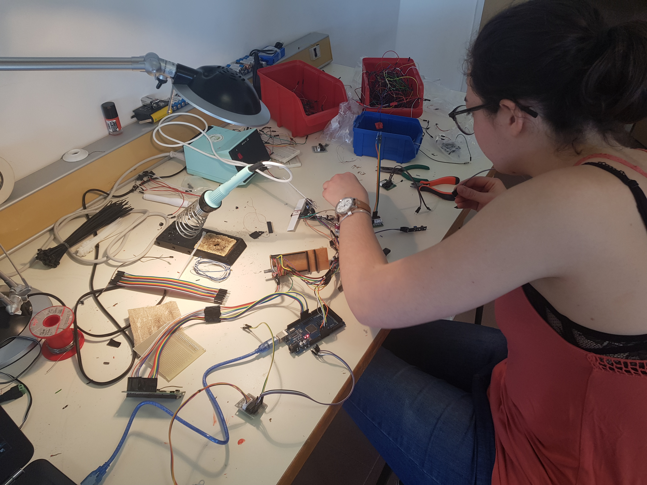
Photos/20190208_111706.jpg
