ClevaPolytech/Arduino-Project/Photos/20190208_111709.jpg

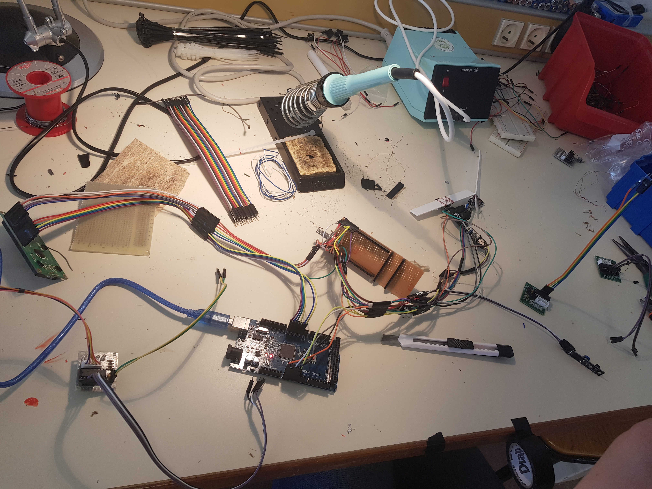
Photos/20190208_111709.jpg
