ClevaPolytech/Arduino-Project/Photos/20190208_111715.jpg

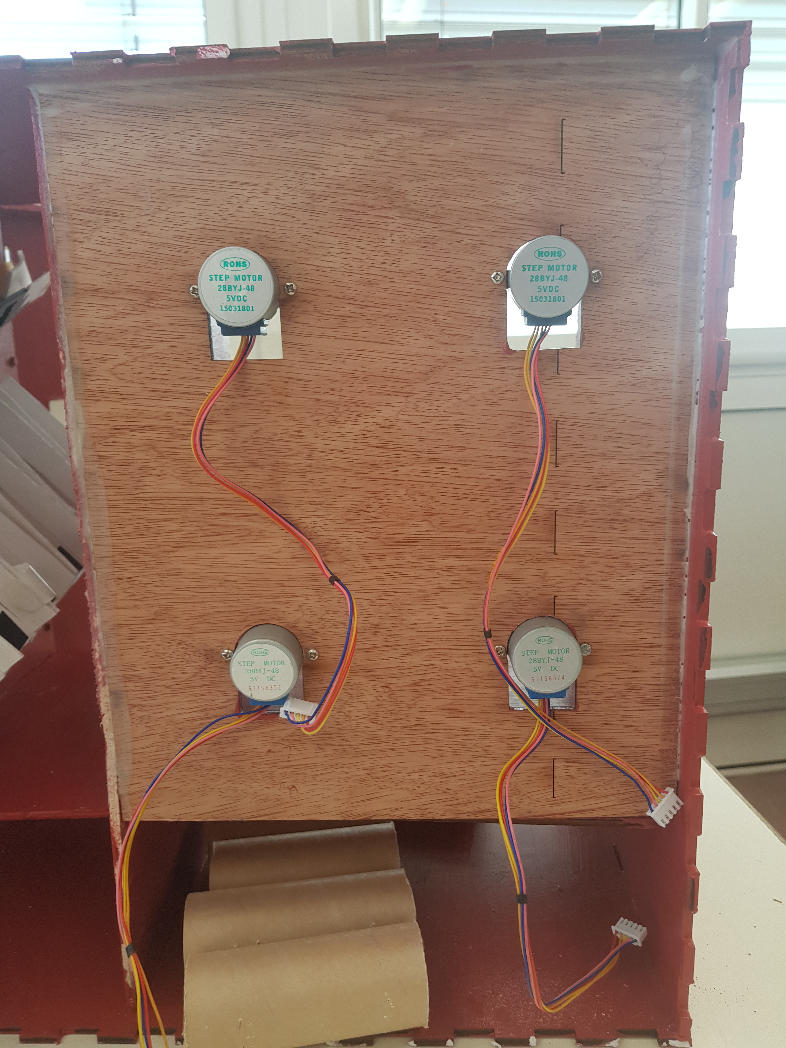
Photos/20190208_111715.jpg
