ClevaPolytech/Arduino-Project/Photos/20190208_111721.jpg

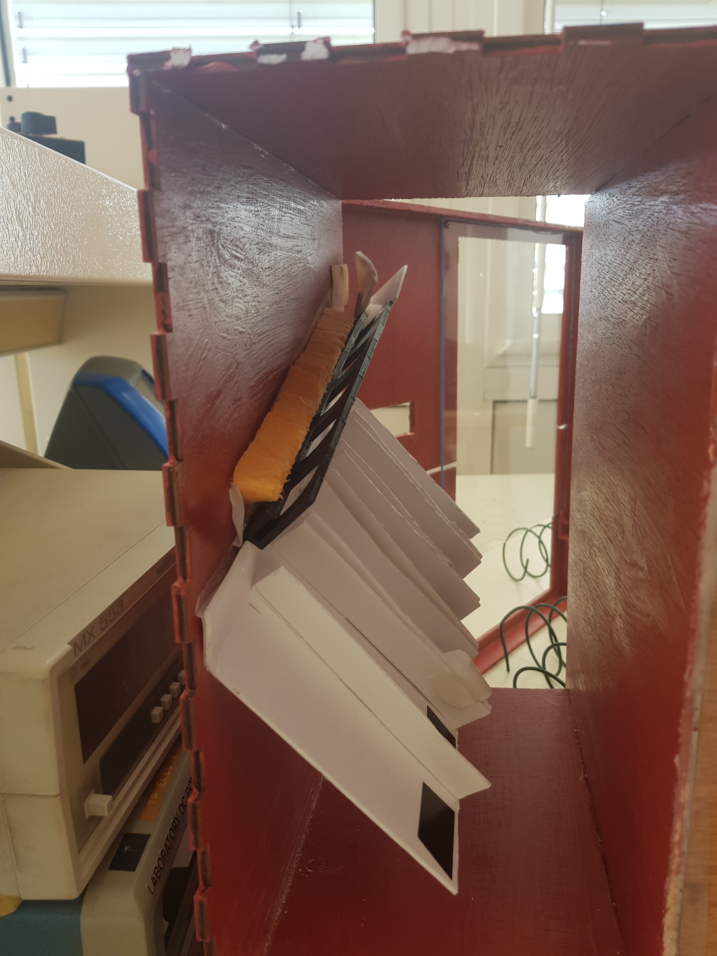
Photos/20190208_111721.jpg
