ClevaPolytech/Arduino-Project/Photos/20190208_111729.jpg

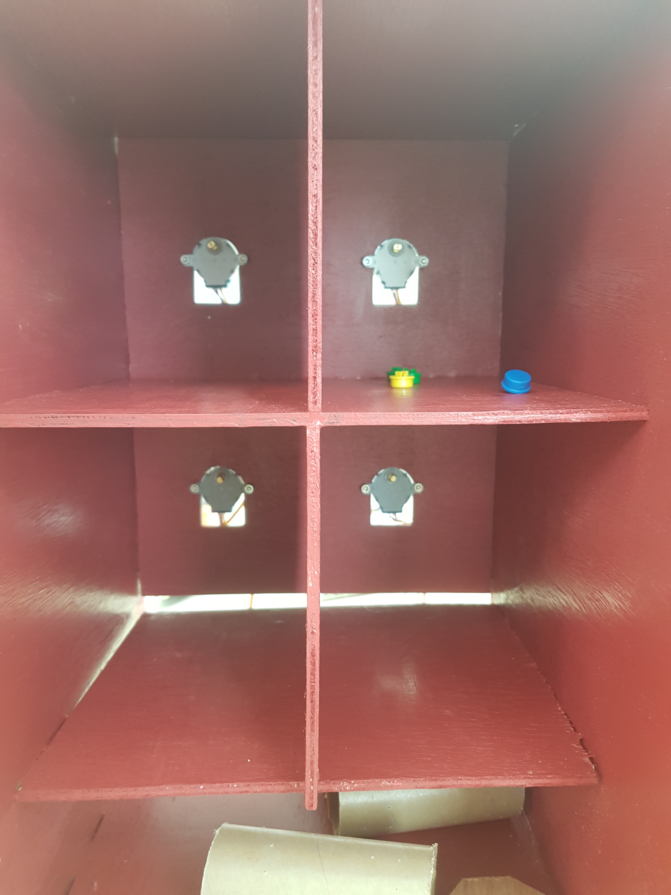
Photos/20190208_111729.jpg
