ClevaPolytech/Arduino-Project/Photos/20190208_195057.jpg

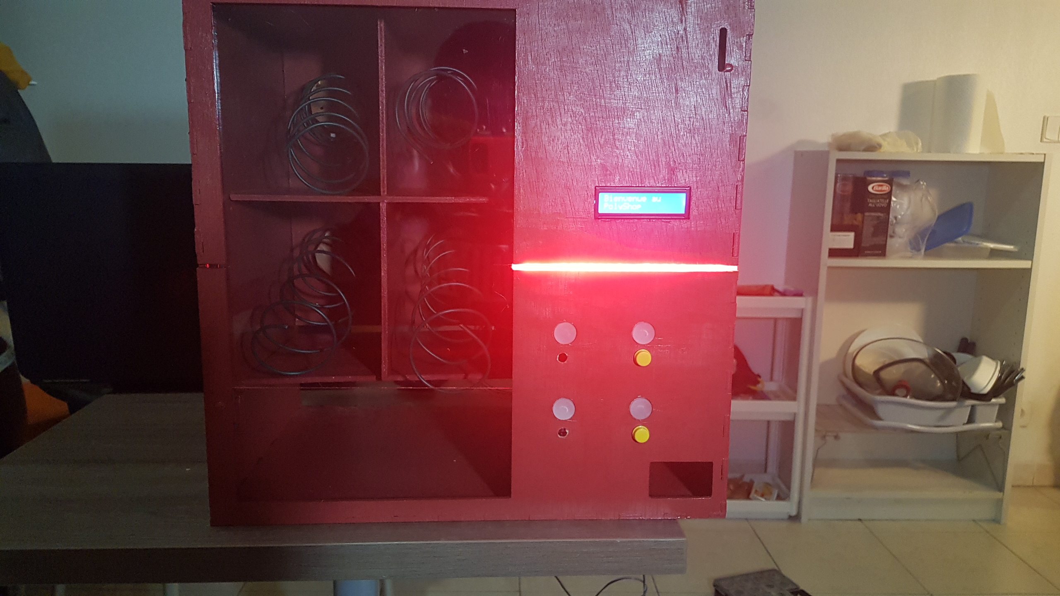
Photos/20190208_195057.jpg
