ClevaPolytech/Arduino-Project/Photos/20190208_200202.jpg

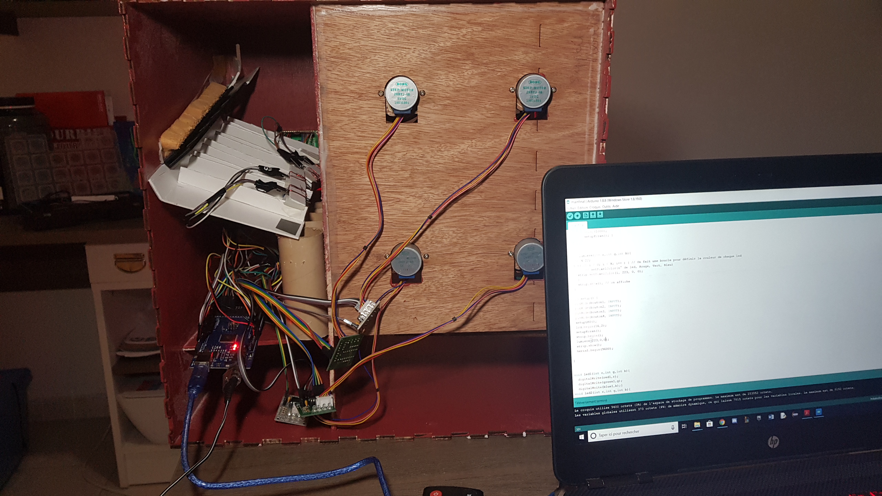
Photos/20190208_200202.jpg
