ClevaPolytech/Arduino-Project/Photos/20190306_163949.jpg

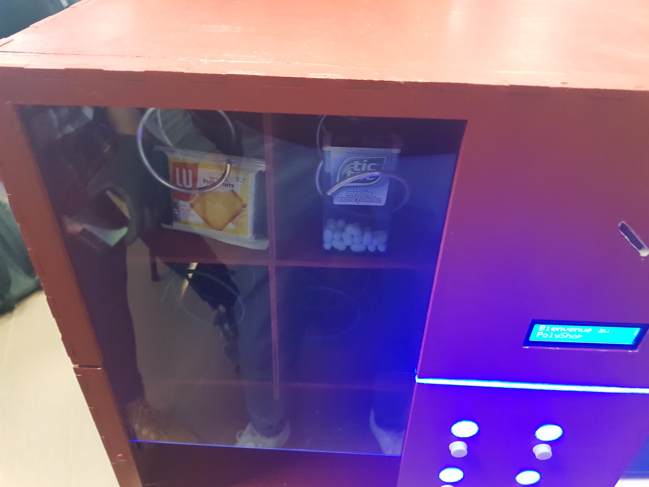
Photos/20190306_163949.jpg
