ClevaPolytech/Arduino-Project/Photos/20190306_165616.jpg

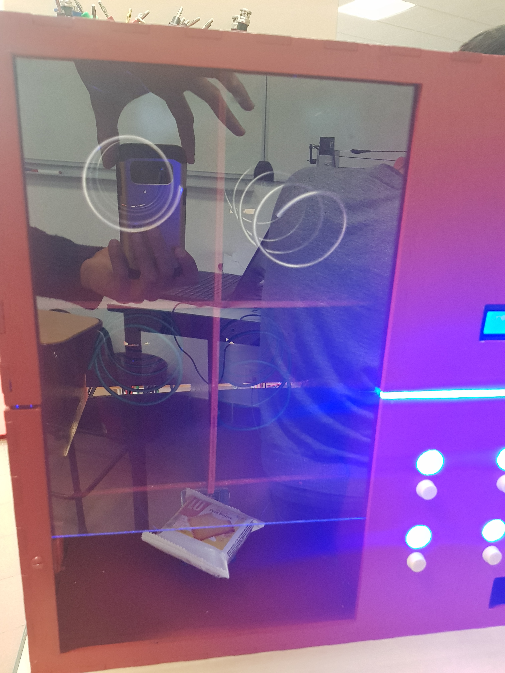
Photos/20190306_165616.jpg
