ClevaPolytech/Arduino-Project/Photos/20190306_165622.jpg

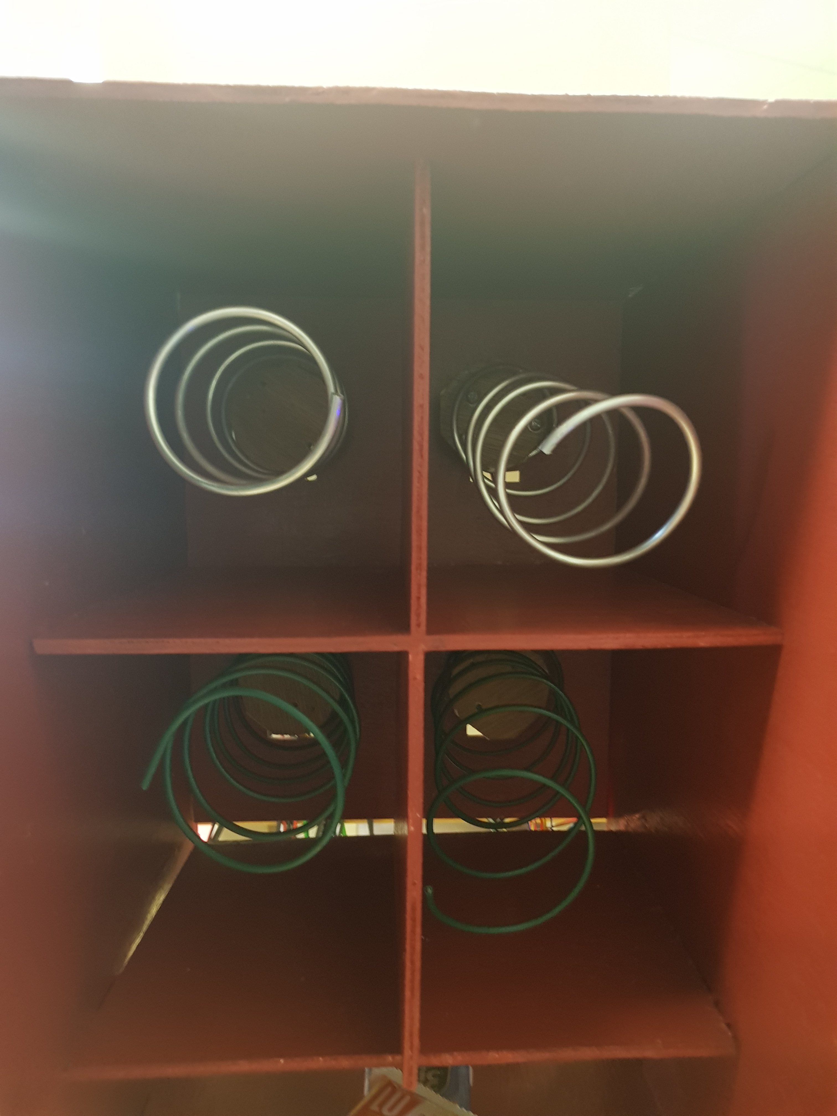
Photos/20190306_165622.jpg
