ClevaPolytech/Arduino-Project/Photos/20190306_165634.jpg

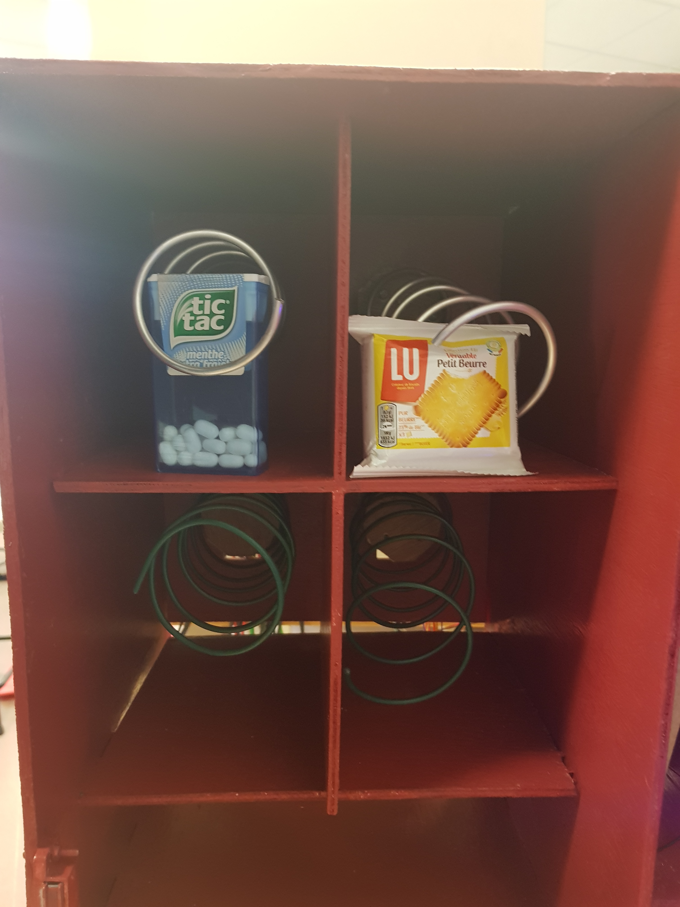
Photos/20190306_165634.jpg
