ClevaPolytech/Arduino-Project/Photos/20190306_165637.jpg

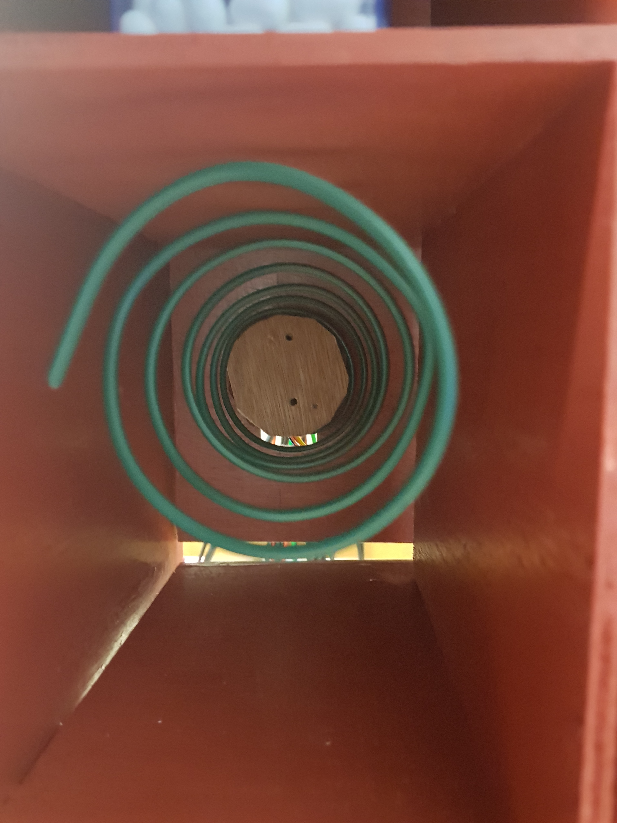
Photos/20190306_165637.jpg
