ClevaPolytech/Arduino-Project/Photos/20190306_165642.jpg

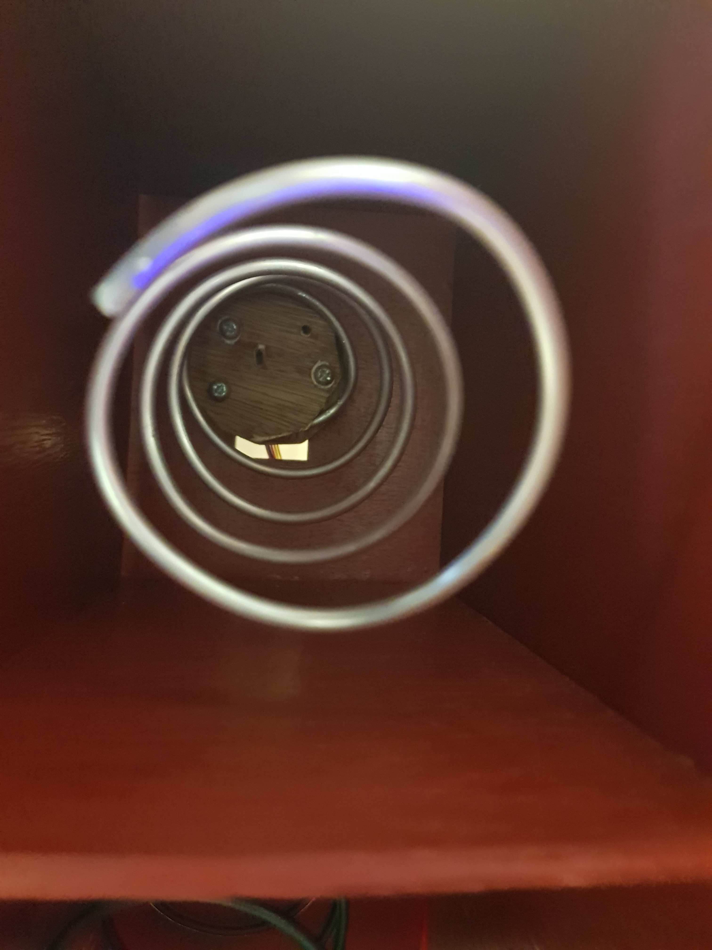
Photos/20190306_165642.jpg
