ClevaPolytech/Arduino-Project/Photos/20190306_165707.jpg

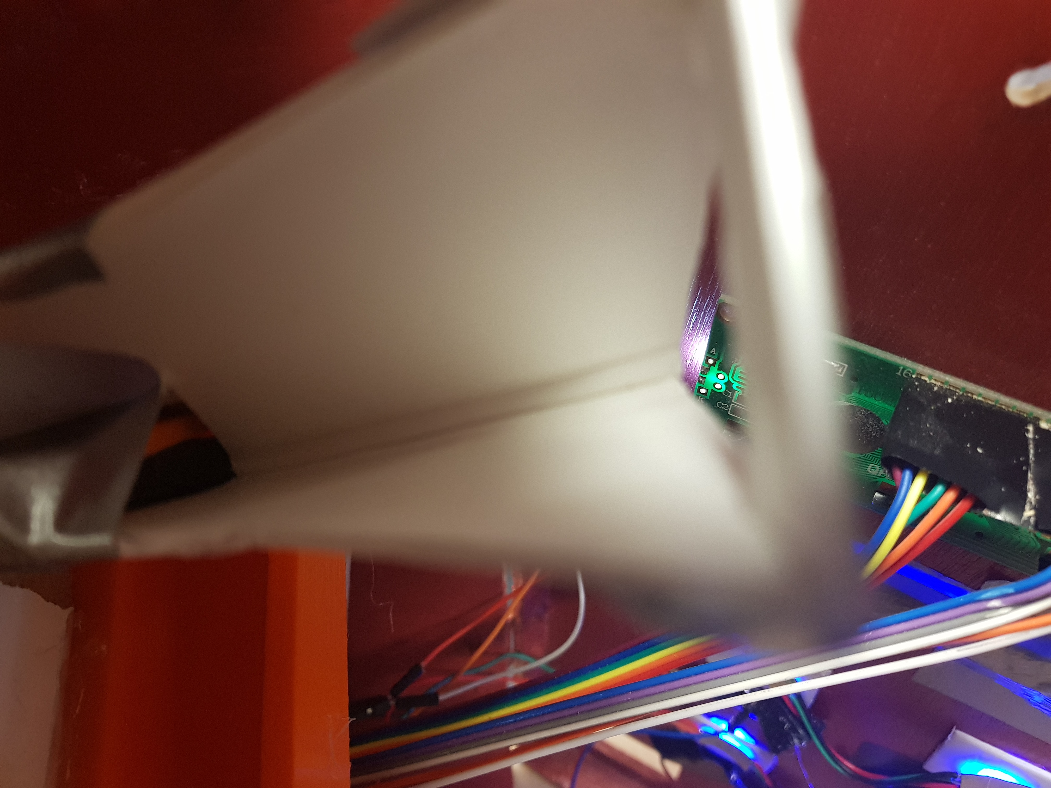
Photos/20190306_165707.jpg
