ClevaPolytech/Arduino-Project/Photos/20190306_165715.jpg

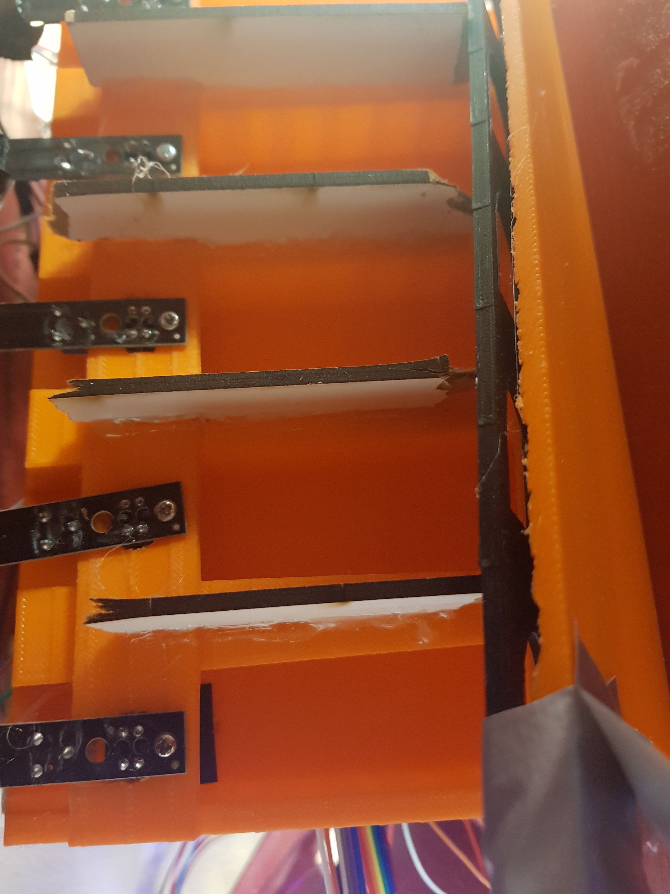
Photos/20190306_165715.jpg
