ClevaPolytech/Arduino-Project/Photos/20190306_165742.jpg

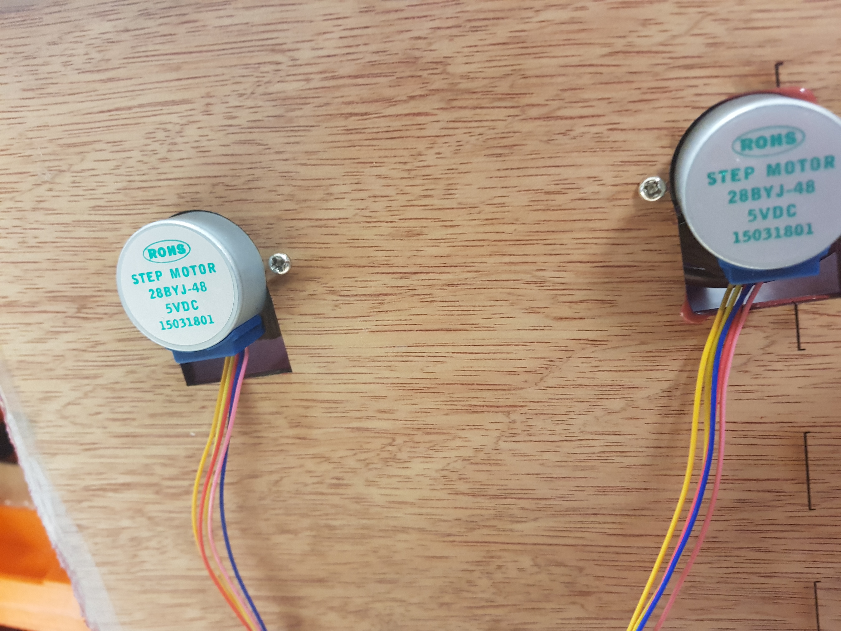
Photos/20190306_165742.jpg
