ClevaPolytech/Arduino-Project/Photos/20190306_165752.jpg

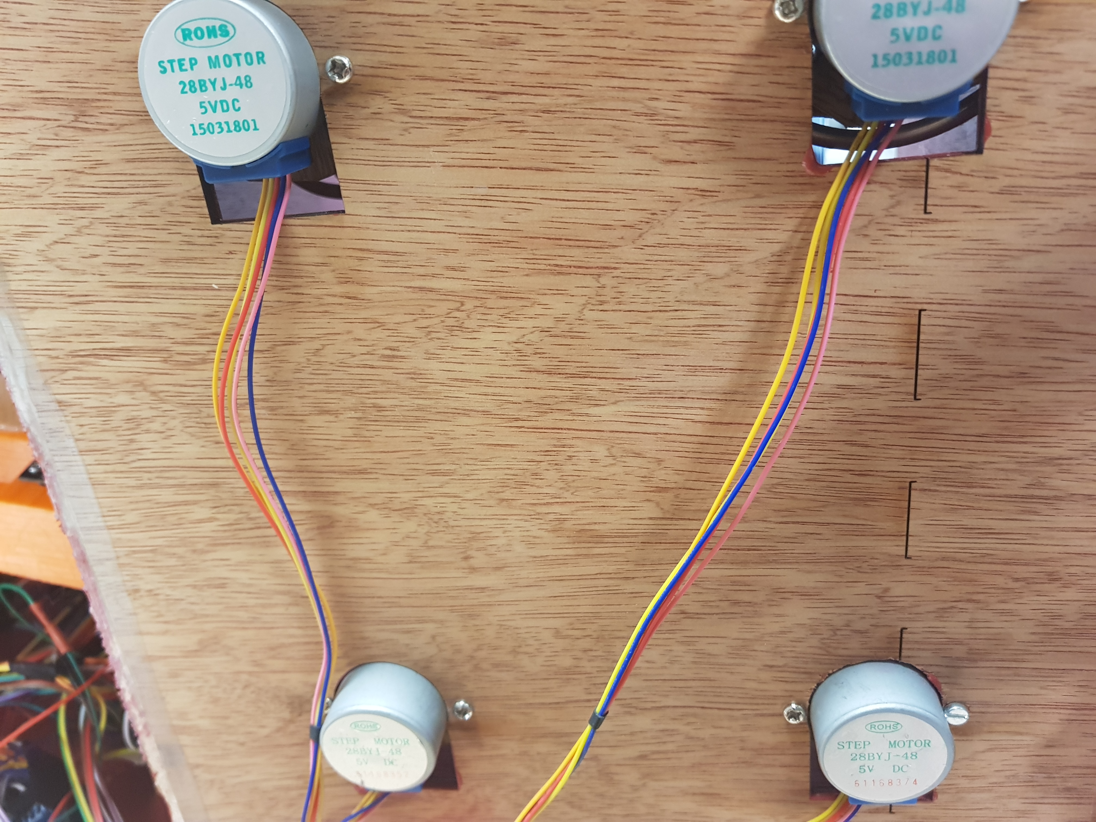
Photos/20190306_165752.jpg
