ClevaPolytech/Arduino-Project/Photos/20190306_165757.jpg

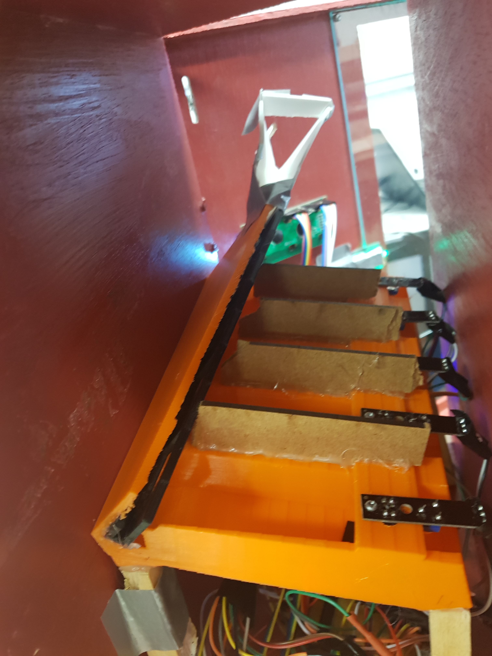
Photos/20190306_165757.jpg
