ClevaPolytech/Arduino-Project/Photos/20190306_165808.jpg

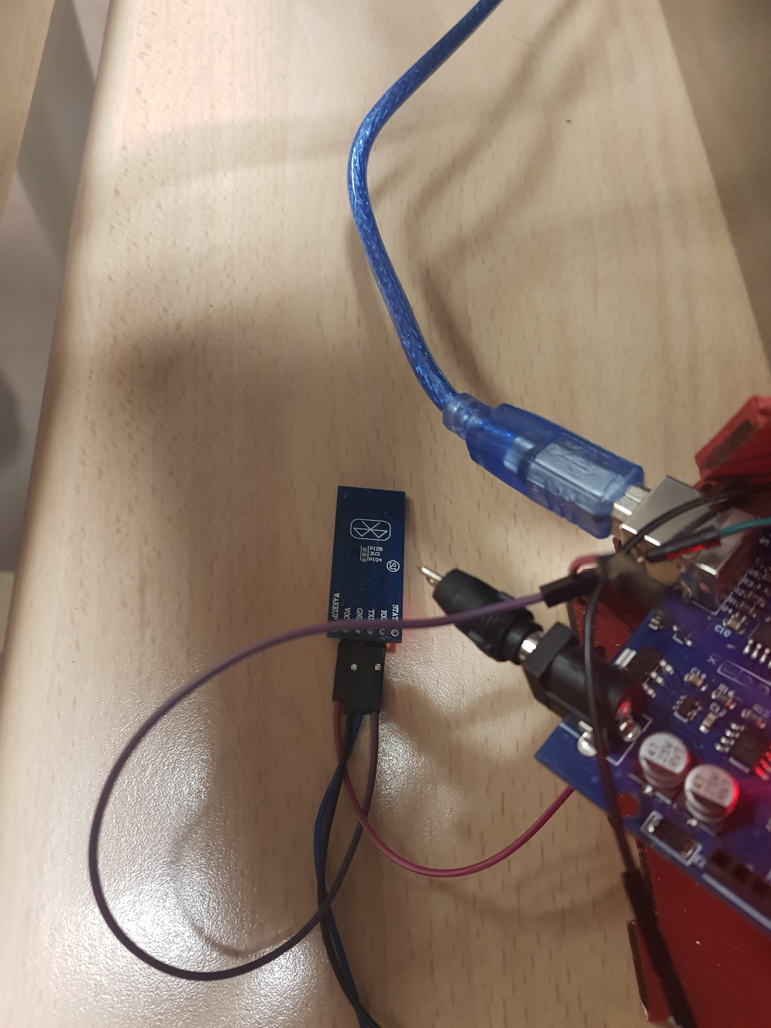
Photos/20190306_165808.jpg
