ClevaPolytech/Arduino-Project/Photos/20190306_170053.jpg

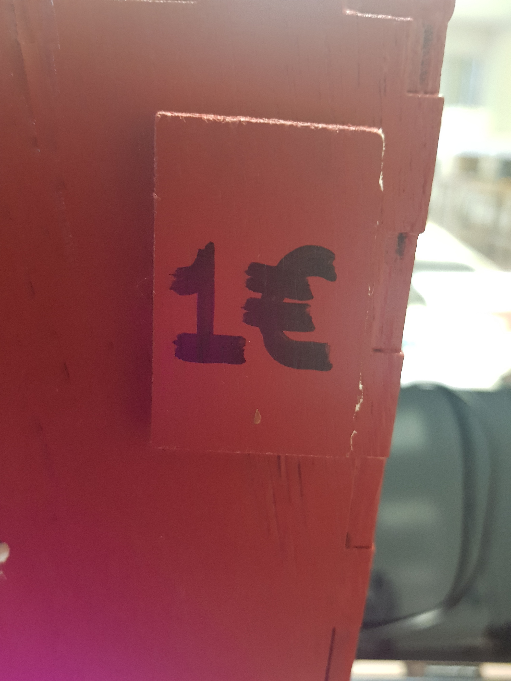
Photos/20190306_170053.jpg
