ClevaPolytech/Arduino-Project/Photos/IMG_20190103_140501.jpg

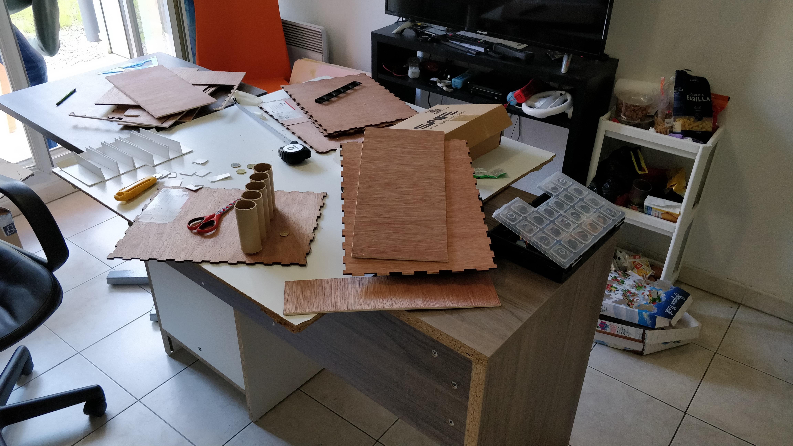
Photos/IMG_20190103_140501.jpg
