ClevaPolytech/Arduino-Project/Photos/IMG_20190103_140515.jpg

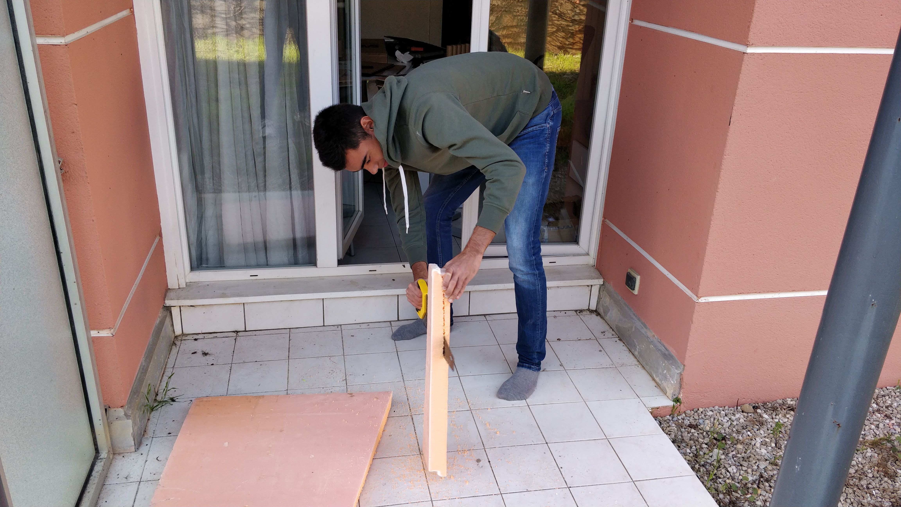
Photos/IMG_20190103_140515.jpg
