ClevaPolytech/Arduino-Project/Photos/IMG_20190103_140516.jpg

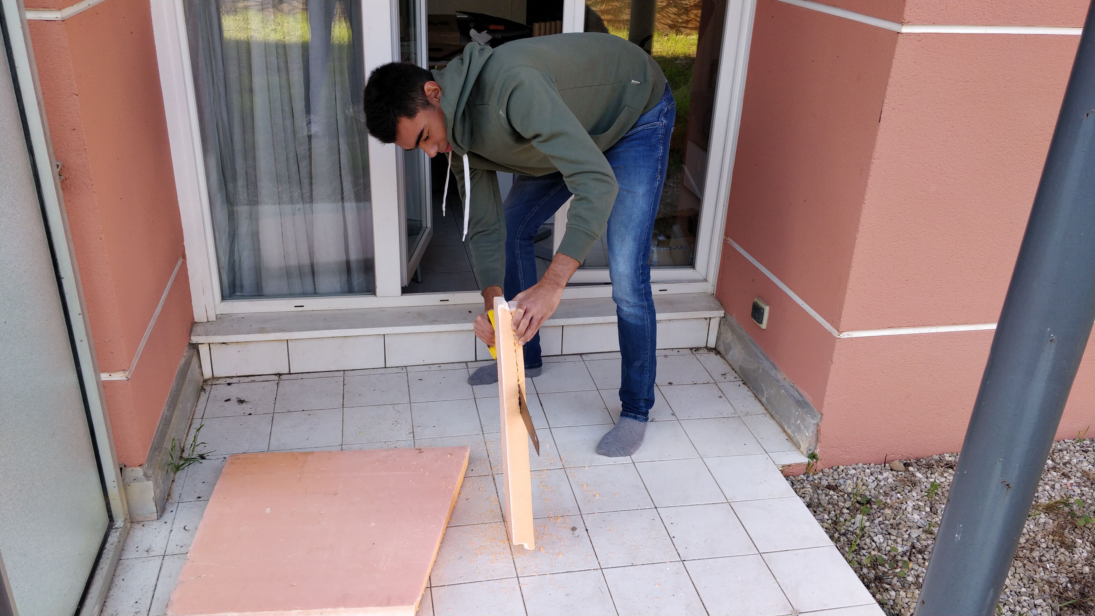
Photos/IMG_20190103_140516.jpg
