ClevaPolytech/Arduino-Project/Photos/IMG_20190103_140525.jpg

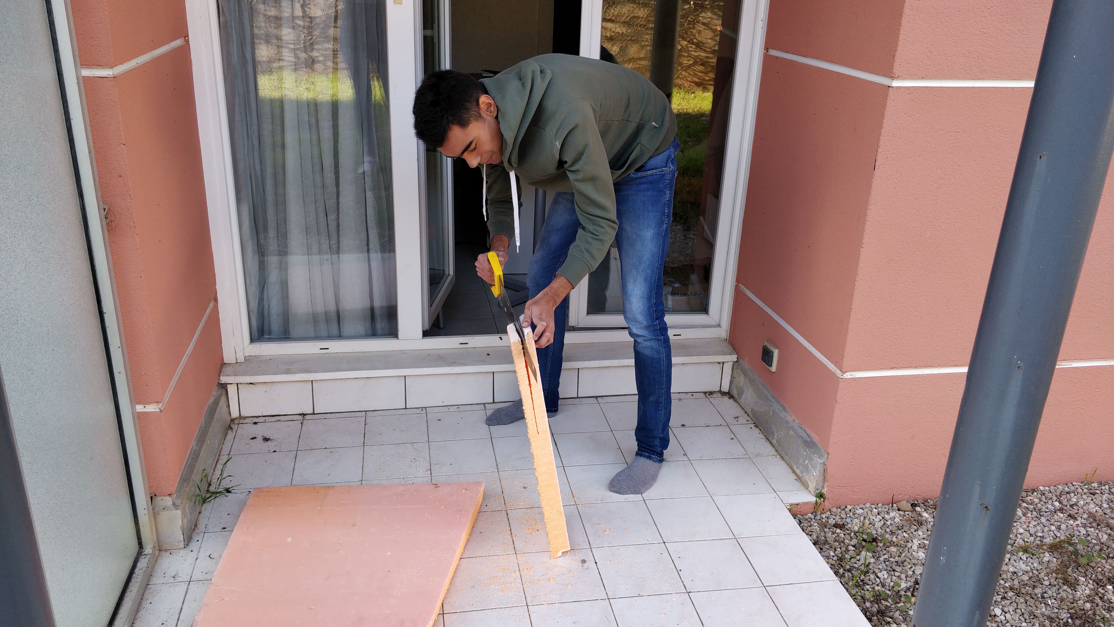
Photos/IMG_20190103_140525.jpg
