ClevaPolytech/Arduino-Project/Photos/IMG_20190103_140527.jpg

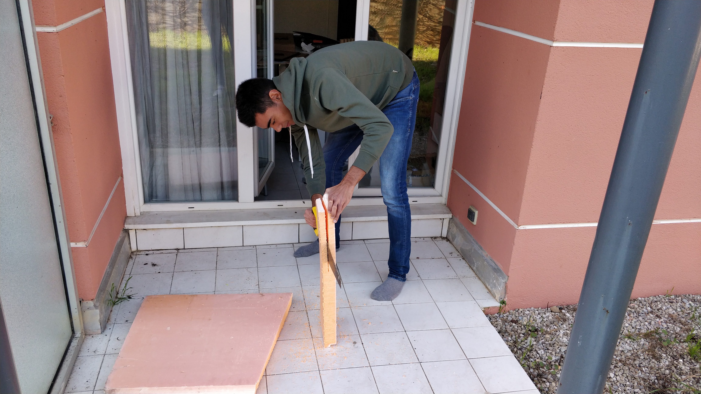
Photos/IMG_20190103_140527.jpg
