ClevaPolytech/Arduino-Project/Photos/IMG_20190103_152406.jpg

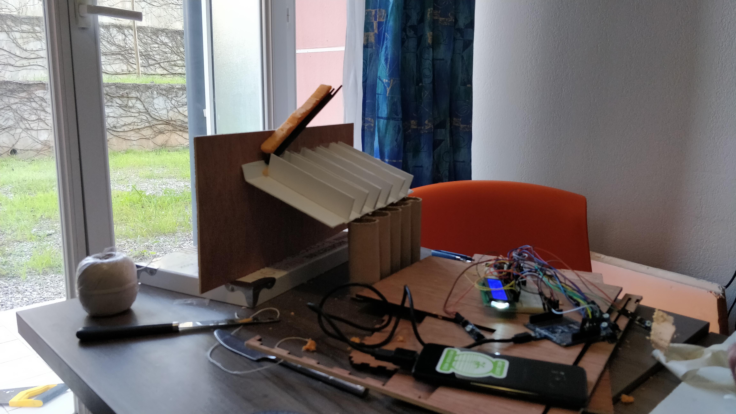
Photos/IMG_20190103_152406.jpg
