ClevaPolytech/Arduino-Project/Photos/IMG_20190103_165508.jpg

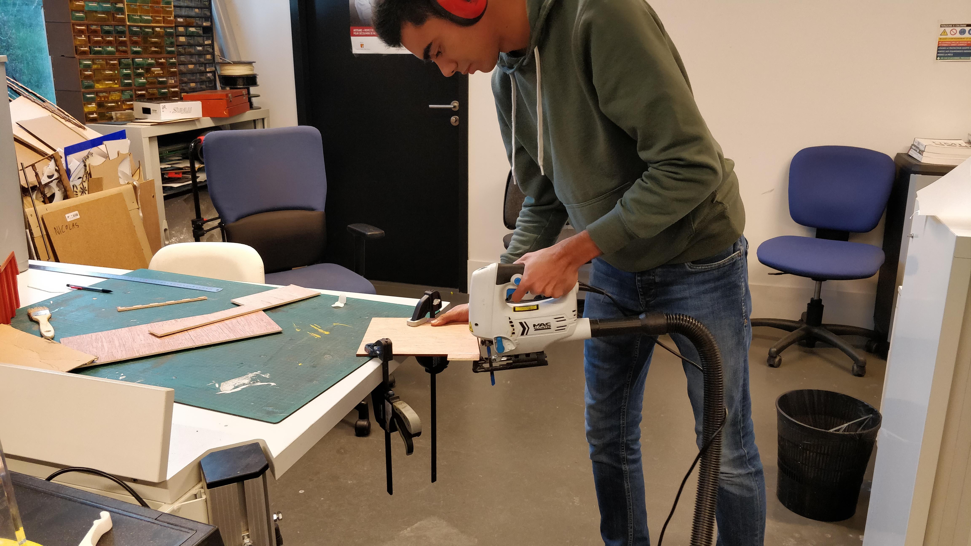
Photos/IMG_20190103_165508.jpg
