ClevaPolytech/Arduino-Project/Photos/IMG_20190107_164547.jpg

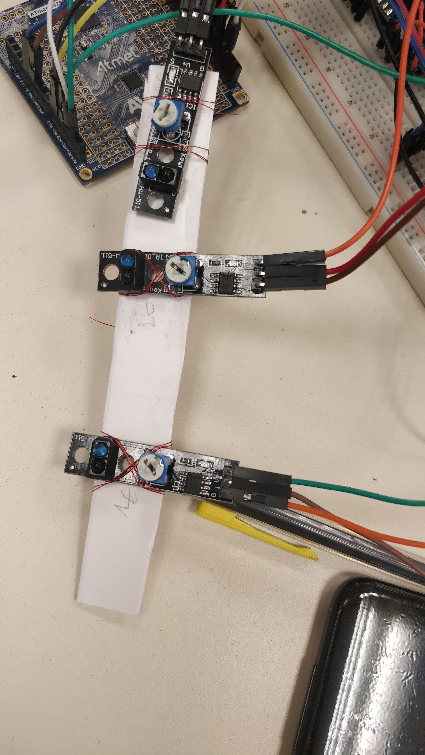
Photos/IMG_20190107_164547.jpg
