ClevaPolytech/Arduino-Project/Photos/IMG_20190107_164558.jpg

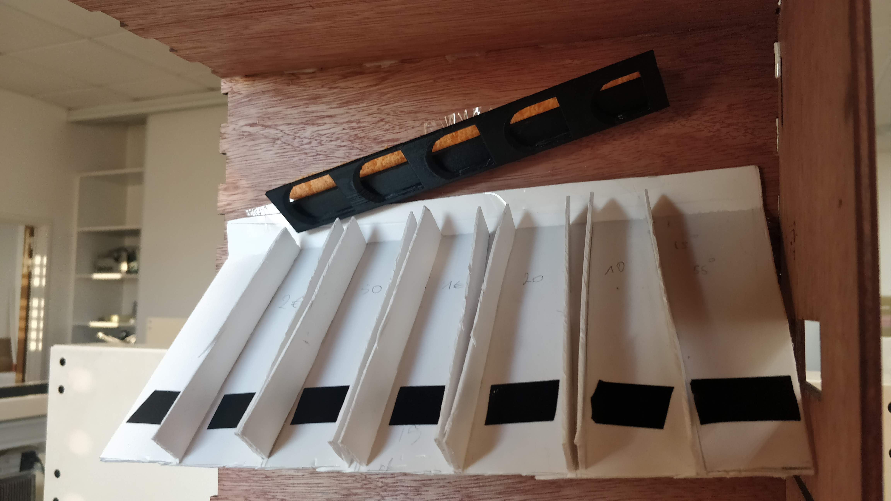
Photos/IMG_20190107_164558.jpg
