ClevaPolytech/Arduino-Project/Photos/IMG_20190107_164601.jpg

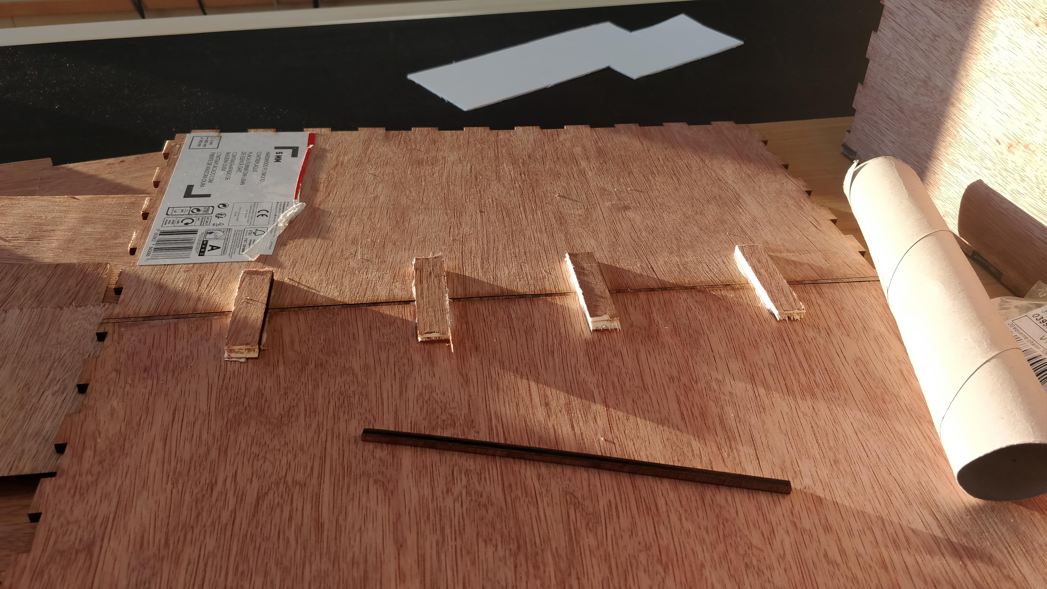
Photos/IMG_20190107_164601.jpg
