ClevaPolytech/Arduino-Project/Photos/IMG_20190107_164820.jpg

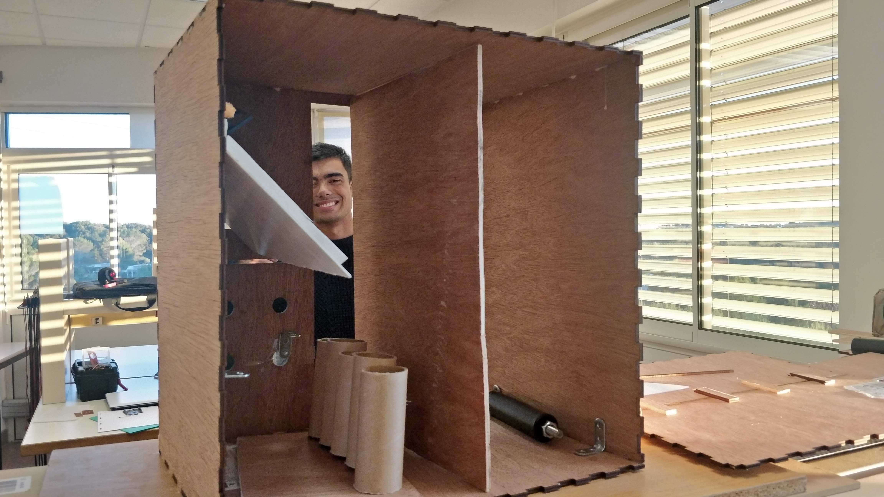
Photos/IMG_20190107_164820.jpg
