ClevaPolytech/Arduino-Project/Photos/IMG_20190301_223052.jpg

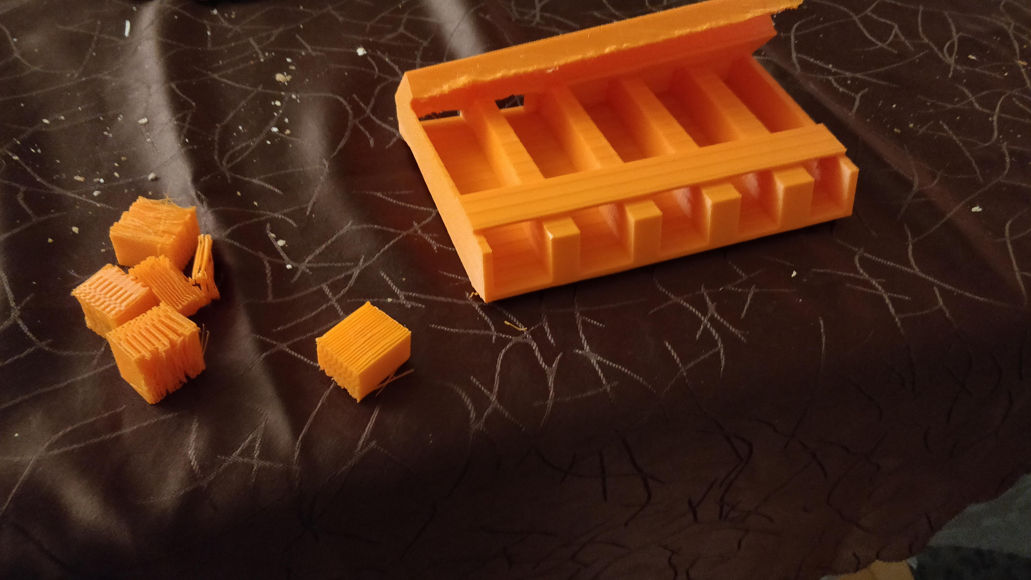
Photos/IMG_20190301_223052.jpg
