ClevaPolytech/Arduino-Project/Photos/IMG_20190306_111258.jpg

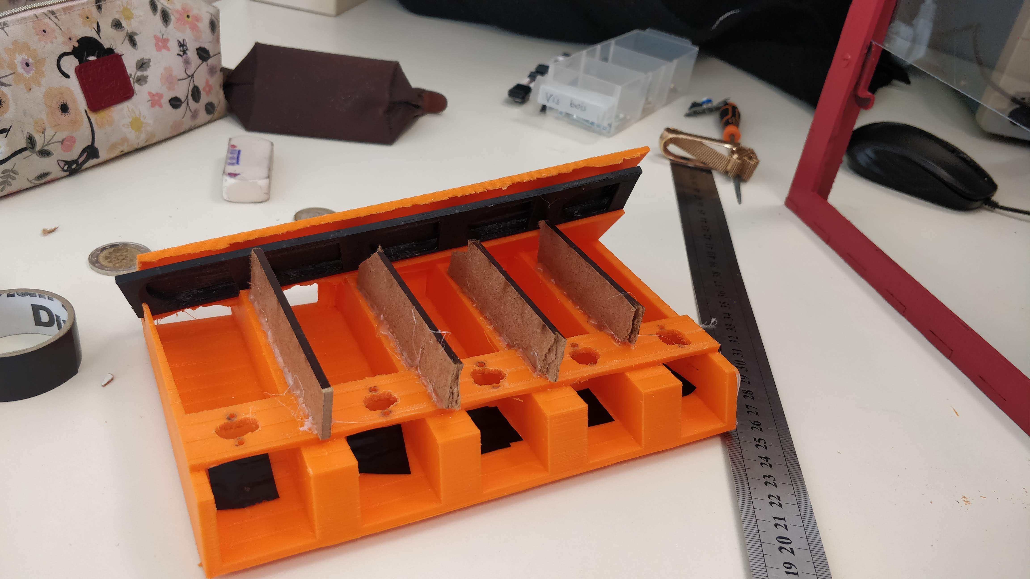
Photos/IMG_20190306_111258.jpg
