ClevaPolytech/Arduino-Project/Photos/IMG_20190306_115111.jpg

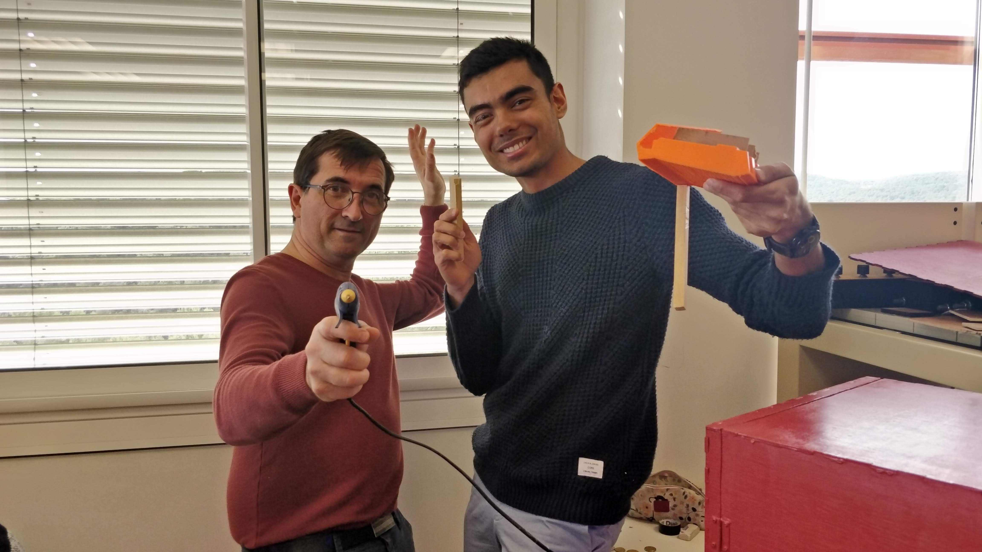
Photos/IMG_20190306_115111.jpg
