ClevaPolytech/Arduino-Project/Photos/IMG_20190306_115129.jpg

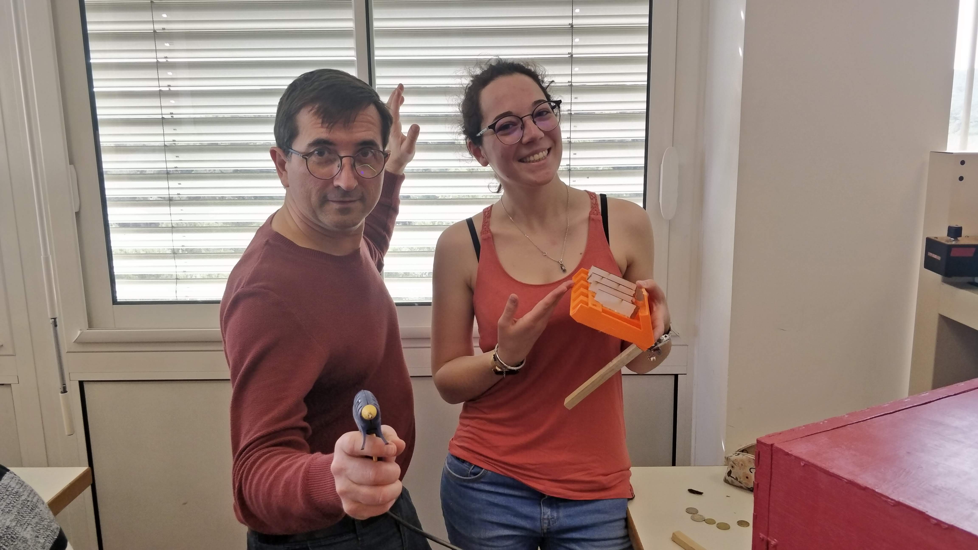
Photos/IMG_20190306_115129.jpg
