ClevaPolytech/Arduino-Project/Photos/IMG_20190306_124428.jpg

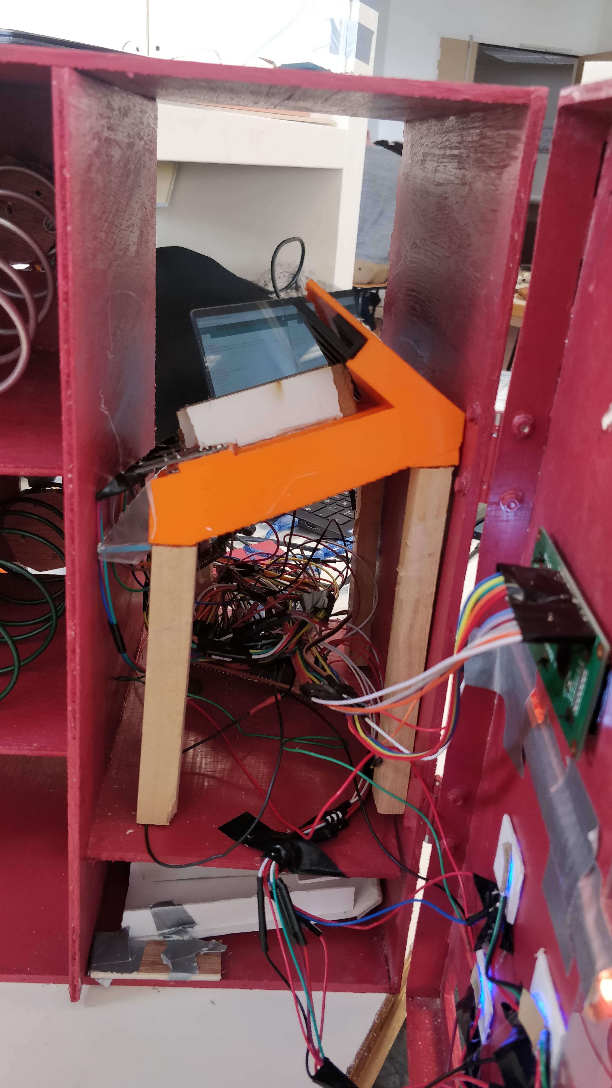
Photos/IMG_20190306_124428.jpg
