ClevaPolytech/Arduino-Project/Photos/IMG_20190306_124438.jpg

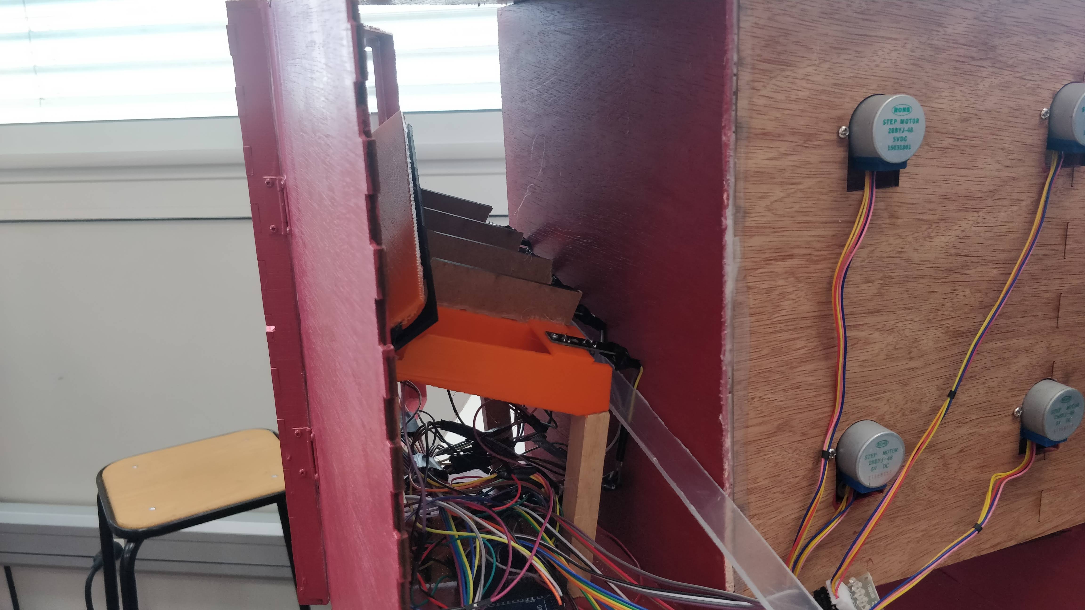
Photos/IMG_20190306_124438.jpg
