ClevaPolytech/Arduino-Project/Photos/20181214_125631.jpg

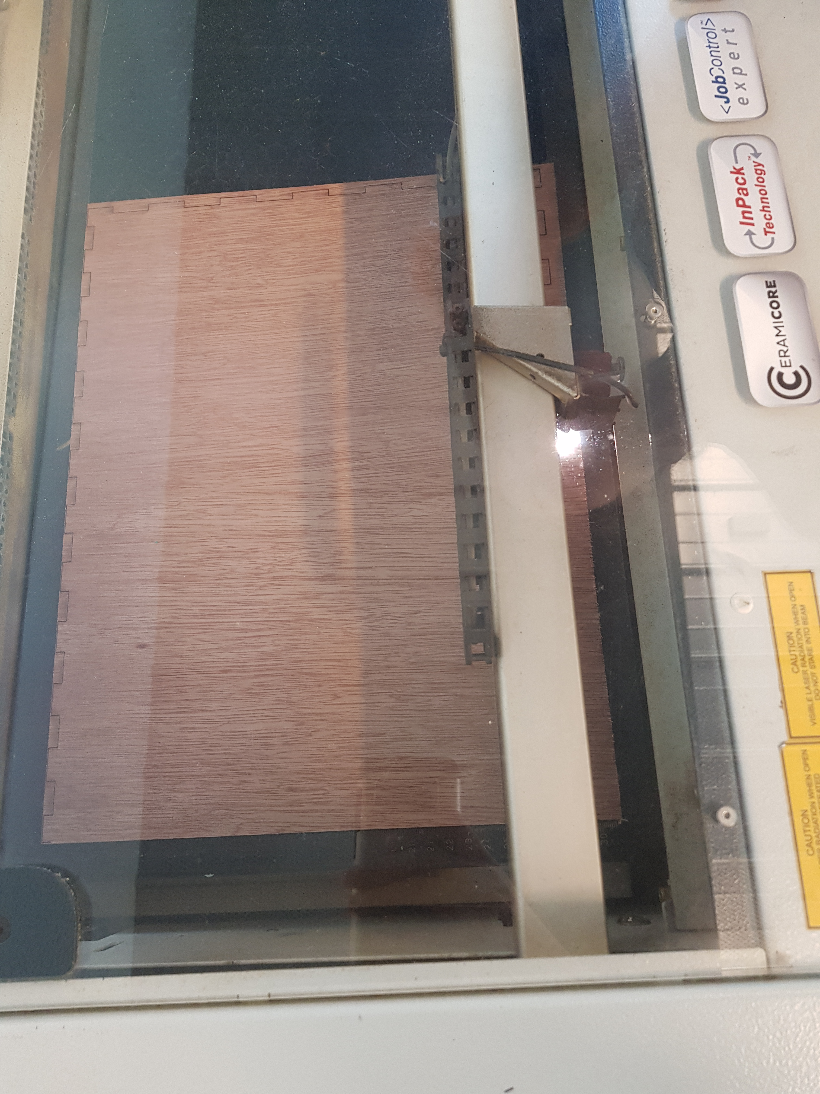
Photos/20181214_125631.jpg
