ClevaPolytech/Arduino-Project/Photos/20181219_125554.jpg

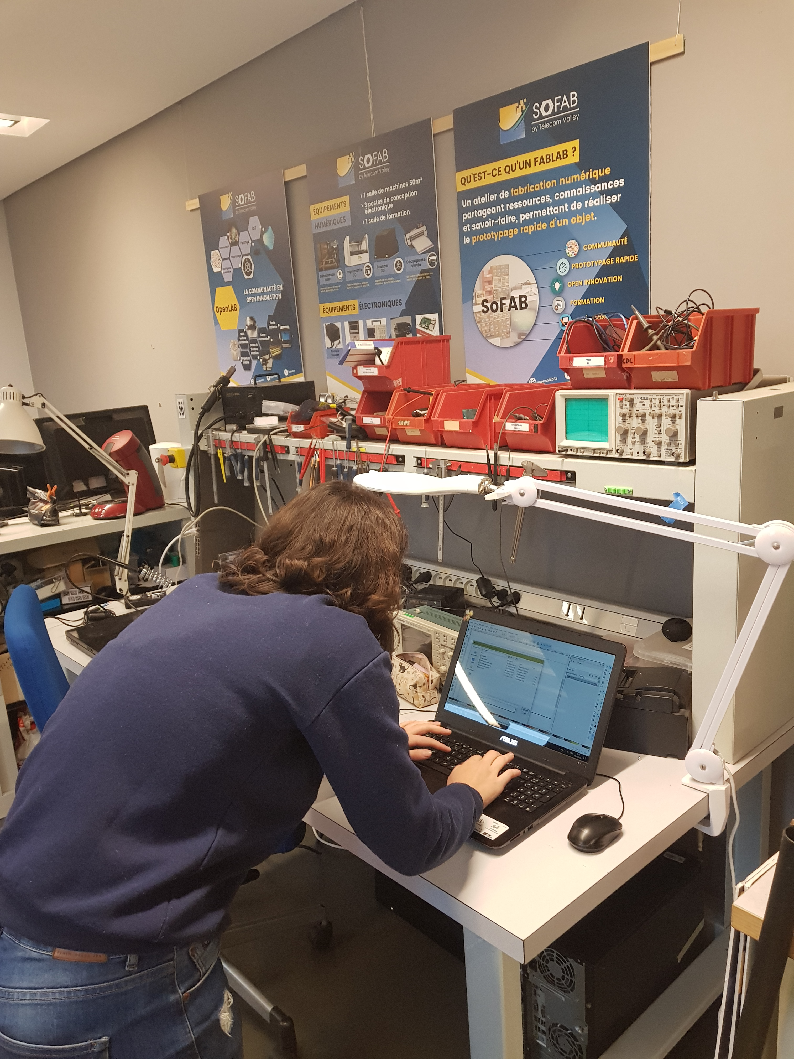
Photos/20181219_125554.jpg
