ClevaPolytech/Arduino-Project/Photos/20181219_131258.jpg

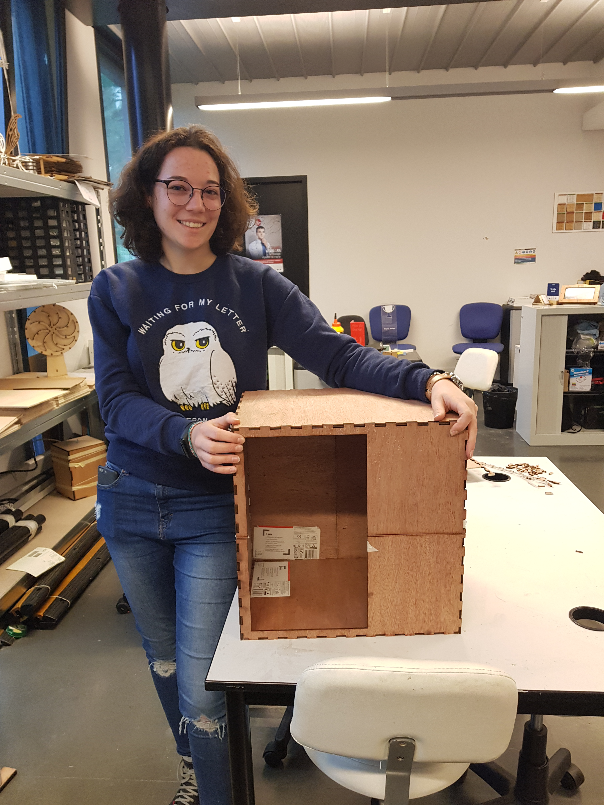
Photos/20181219_131258.jpg
