ClevaPolytech/Arduino-Project/Photos/20190306_130153.jpg

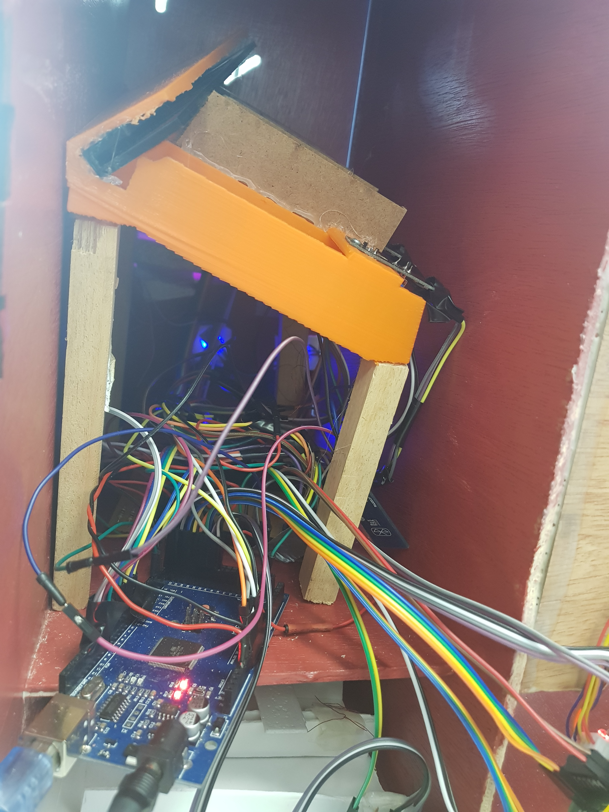
Photos/20190306_130153.jpg
