ClevaPolytech/Arduino-Project/Photos/20190306_130200.jpg

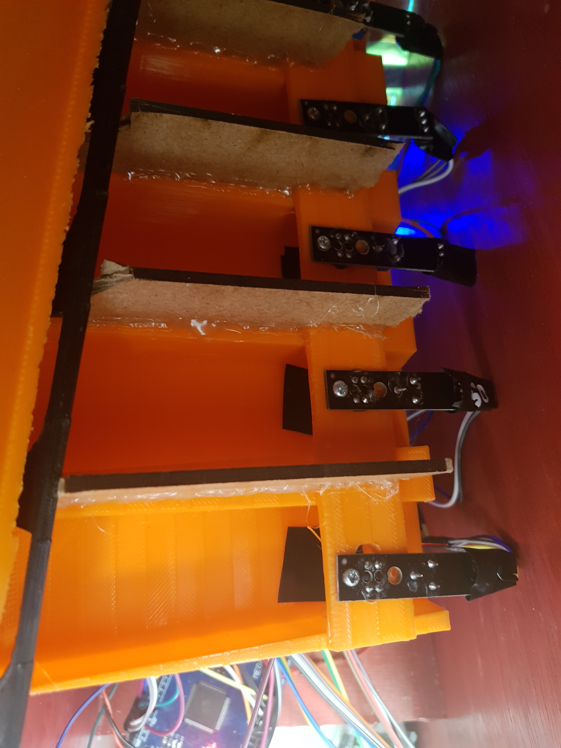
Photos/20190306_130200.jpg
