ClevaPolytech/Arduino-Project/Photos/20190306_165709.jpg

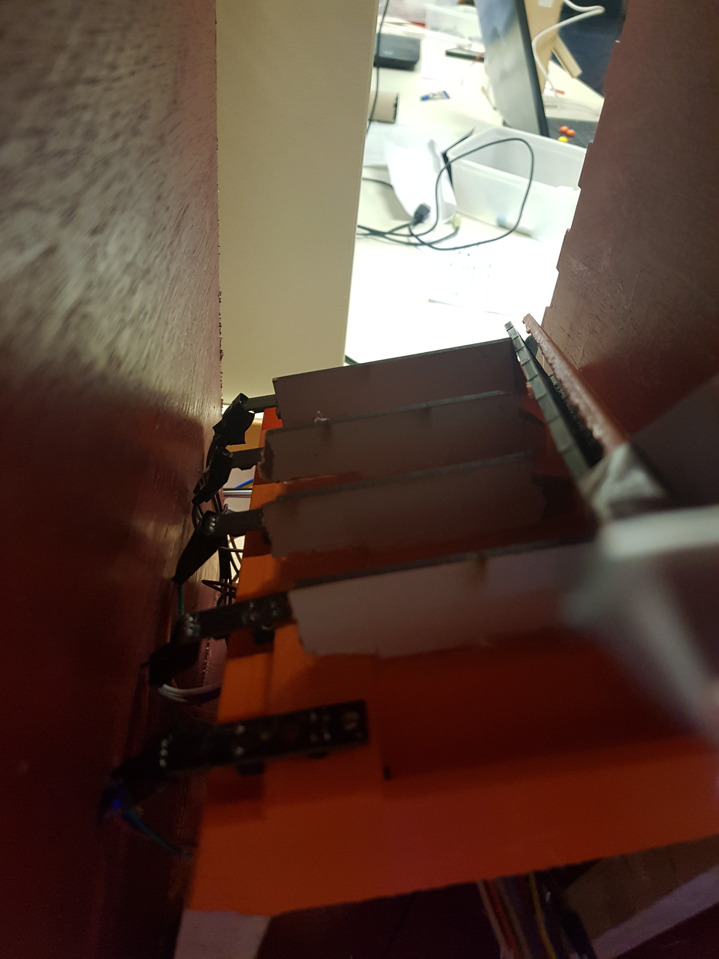
Photos/20190306_165709.jpg
