ClevaPolytech/Arduino-Project/Photos/20190306_165728.jpg

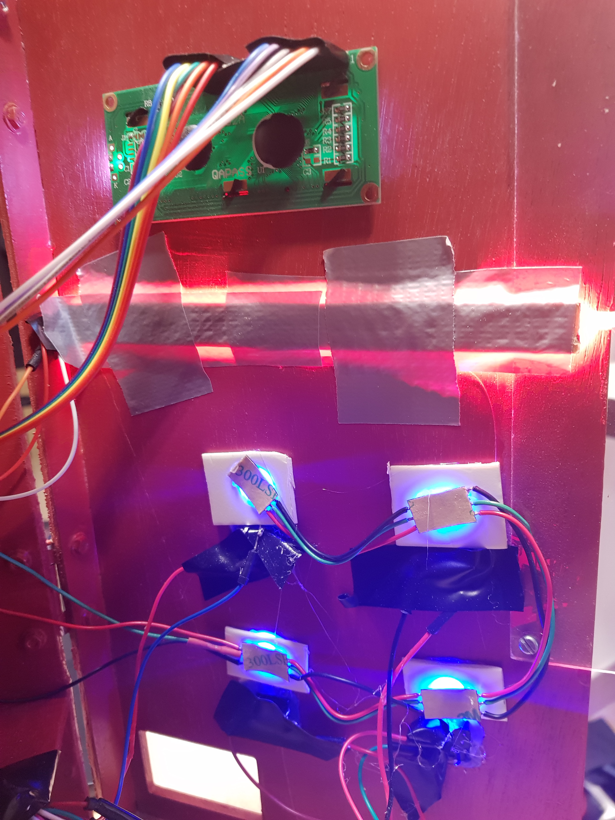
Photos/20190306_165728.jpg
