ClevaPolytech/Arduino-Project/Photos/20190306_165802.jpg

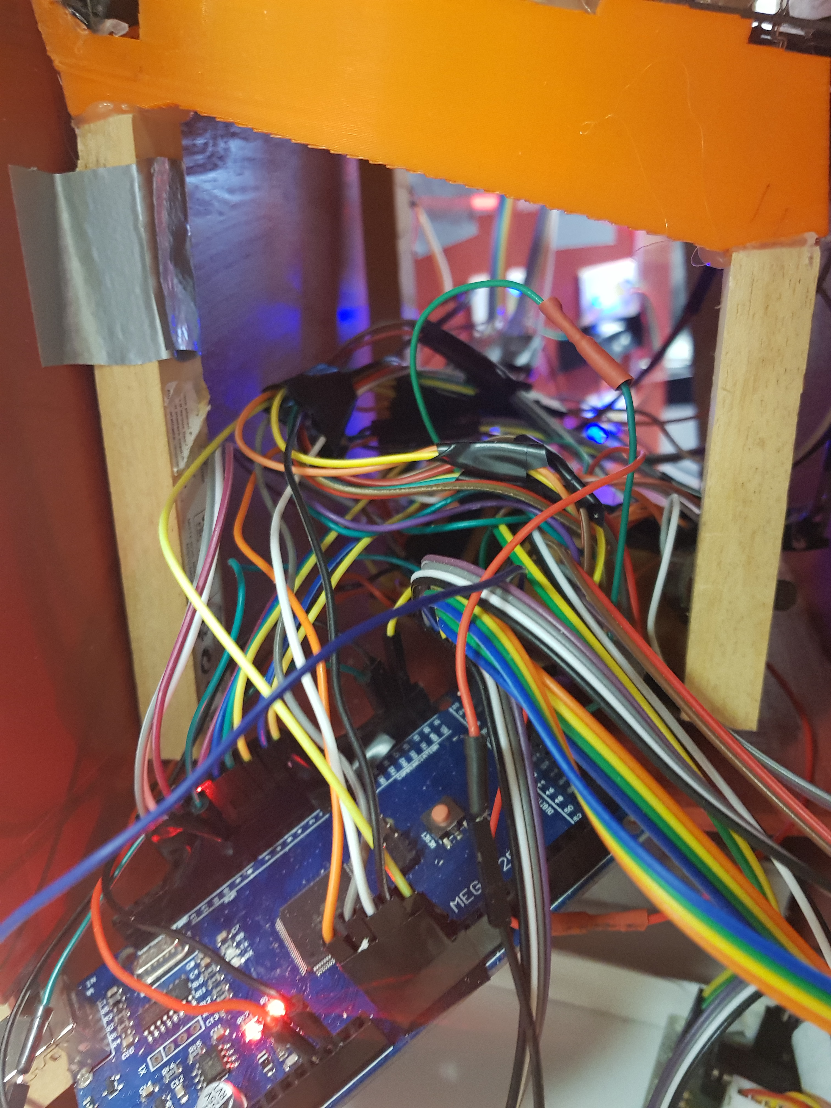
Photos/20190306_165802.jpg
