ClevaPolytech/Arduino-Project/Photos/20190306_165805.jpg

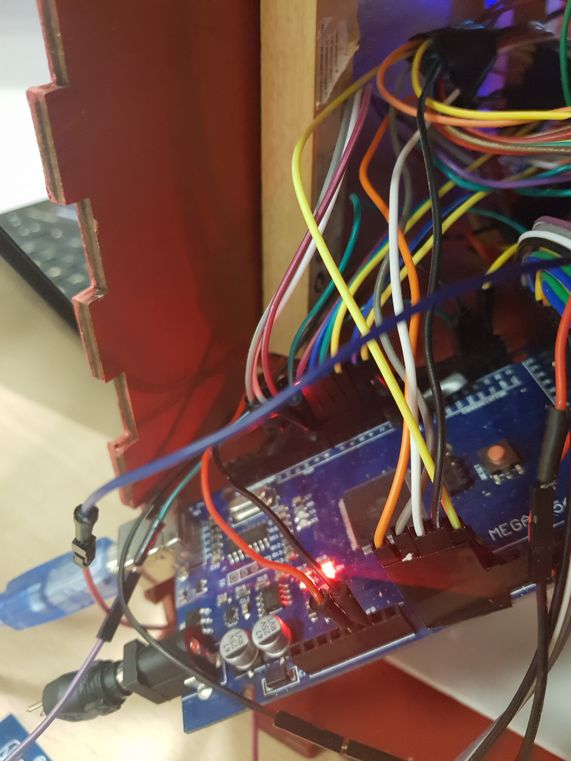
Photos/20190306_165805.jpg
