ClevaPolytech/Arduino-Project/Photos/20190306_170059.jpg

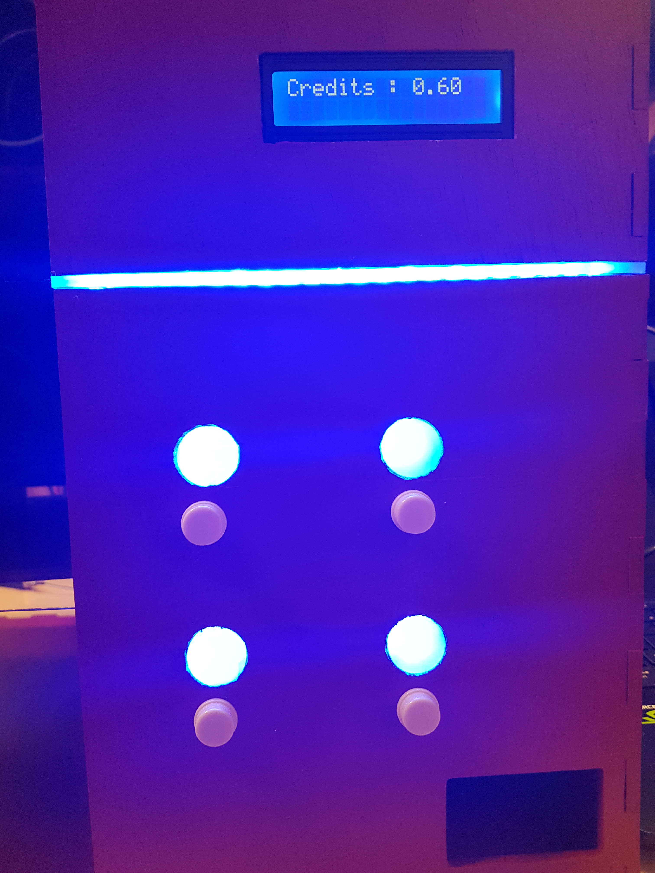
Photos/20190306_170059.jpg
